Techposts/TankSync/docs/firmware/screenshots/flasher/flasher-1.png

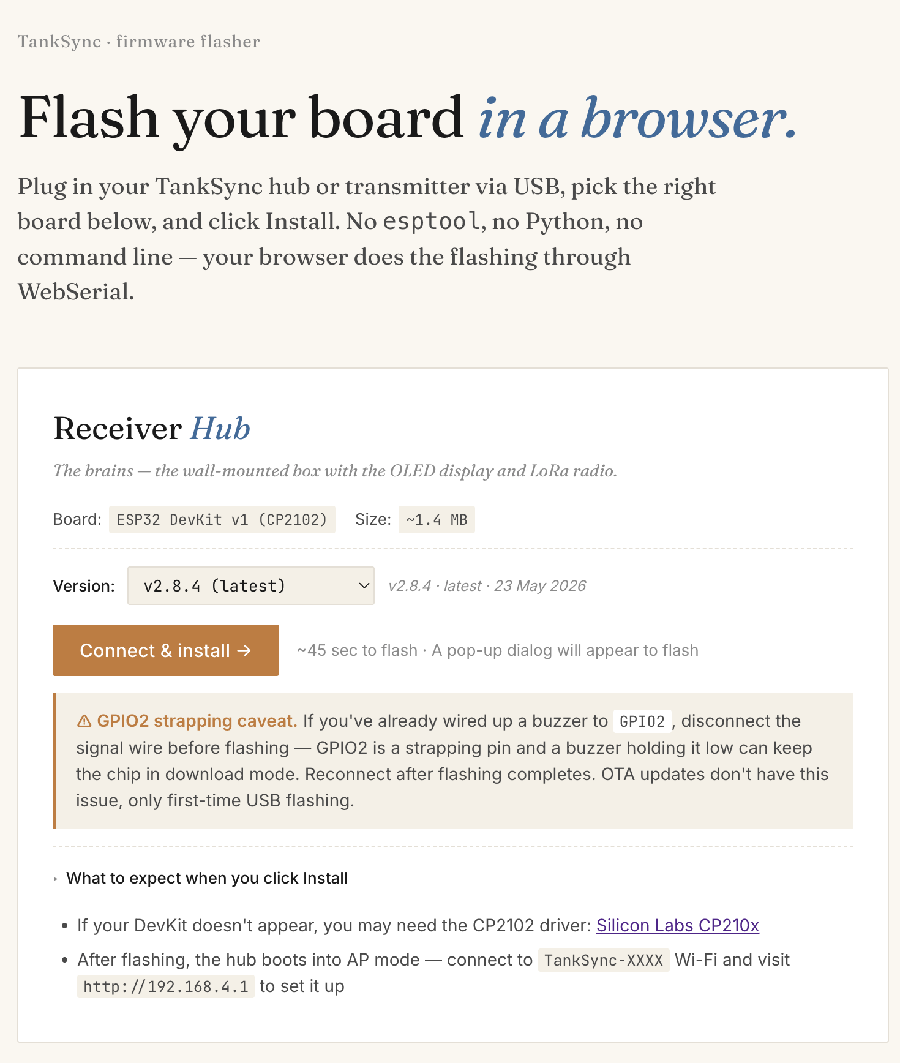
docs/firmware/screenshots/flasher/flasher-1.png
