Techposts/TankSync/docs/firmware/screenshots/flasher/flasher-2.png

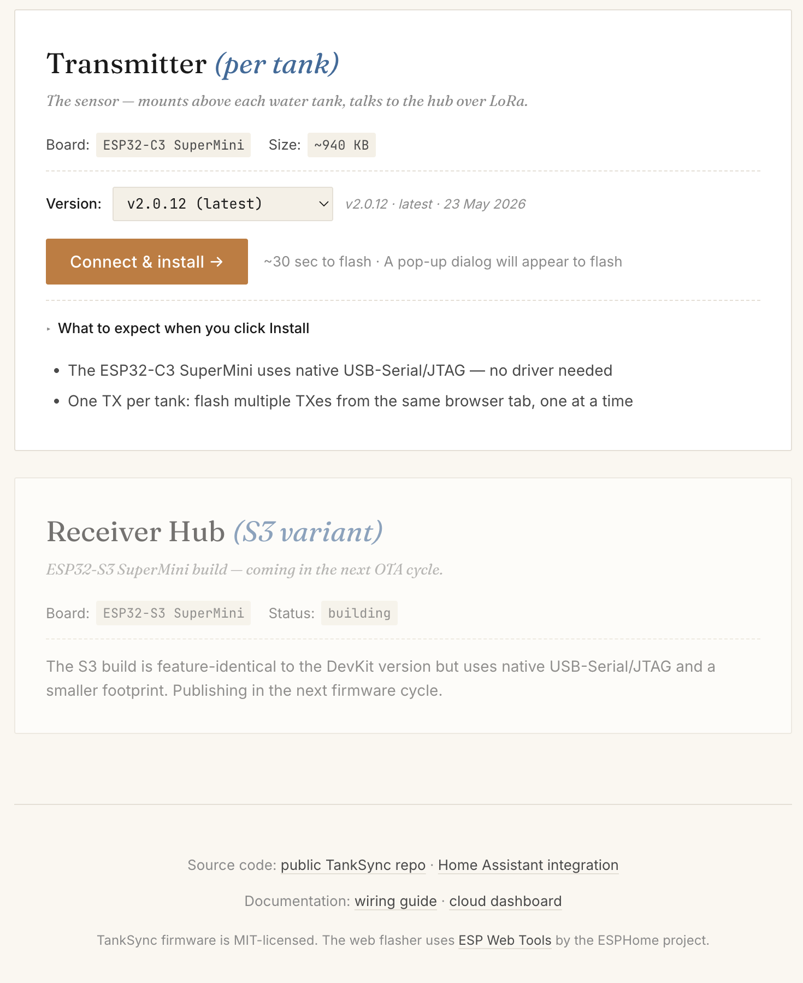
docs/firmware/screenshots/flasher/flasher-2.png
