Techposts/TankSync/docs/firmware/screenshots/pwa/alerts-feed-dark.png

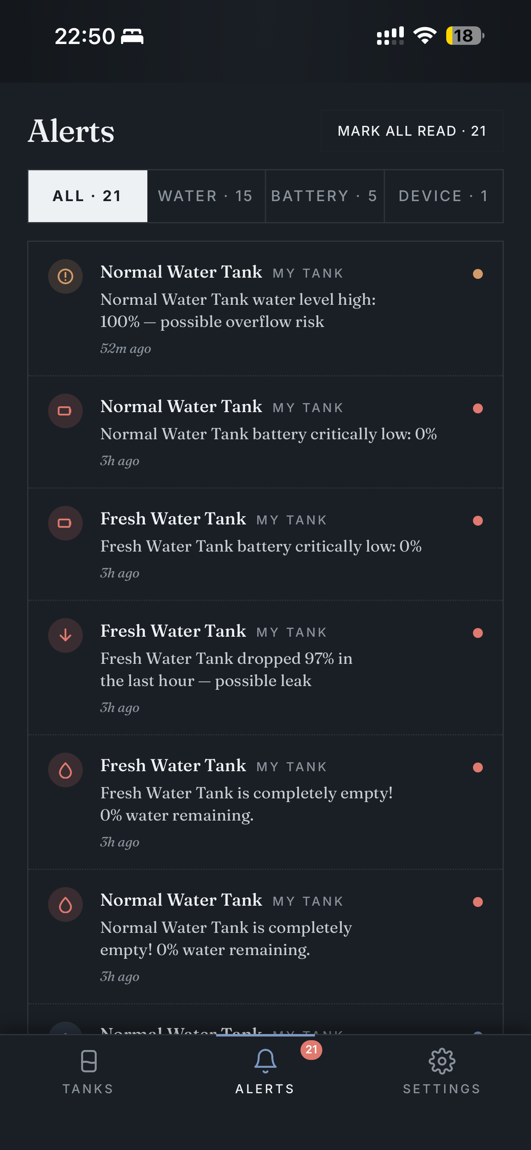
docs/firmware/screenshots/pwa/alerts-feed-dark.png
