Techposts/TankSync/docs/firmware/screenshots/pwa/alerts-feed-light.png

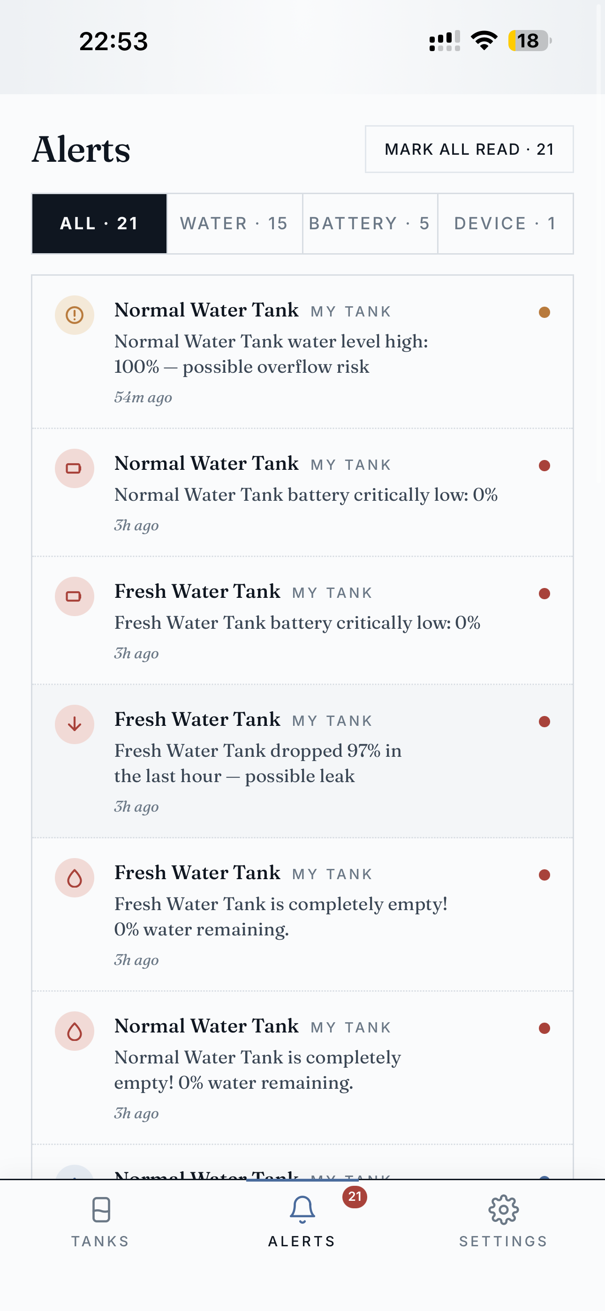
docs/firmware/screenshots/pwa/alerts-feed-light.png
