Techposts/TankSync/docs/firmware/screenshots/pwa/dashboard-light.png

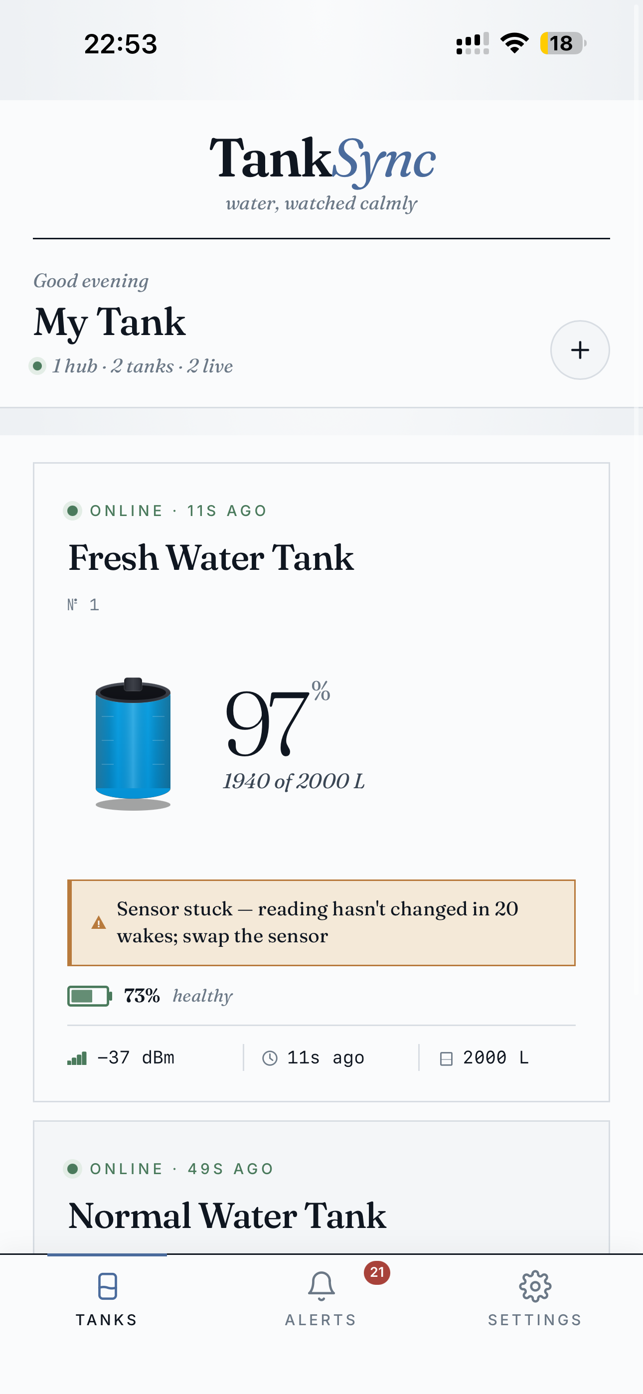
docs/firmware/screenshots/pwa/dashboard-light.png
