Techposts/TankSync/docs/firmware/screenshots/pwa/dashboard-sensor-stuck-warning.png

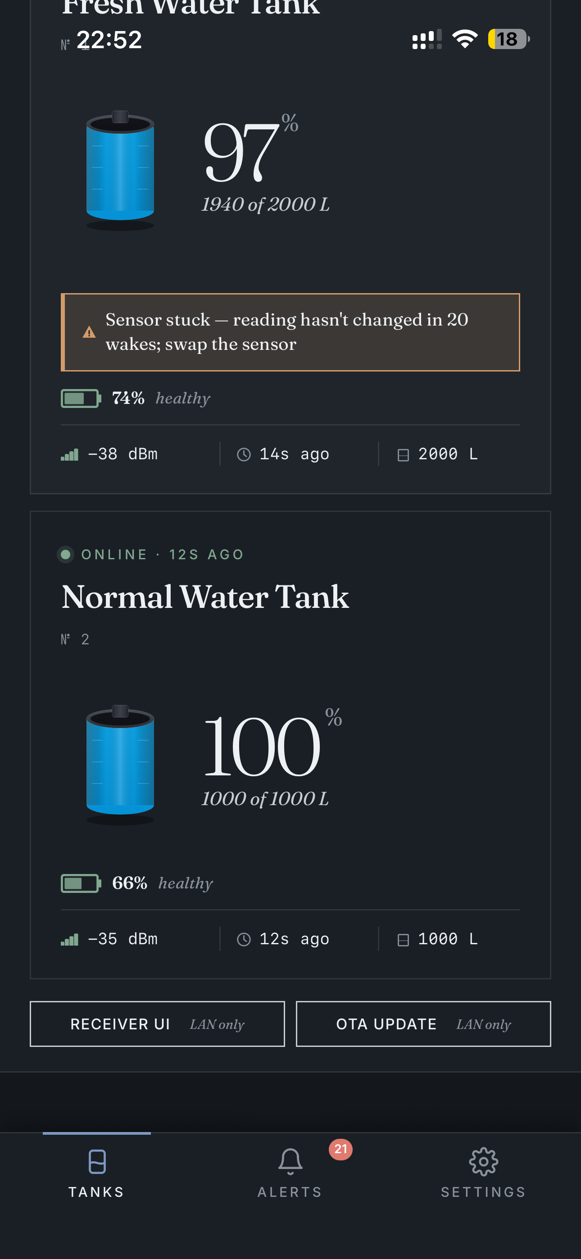
docs/firmware/screenshots/pwa/dashboard-sensor-stuck-warning.png
