Techposts/TankSync/docs/firmware/screenshots/pwa/firmware-update-page.png

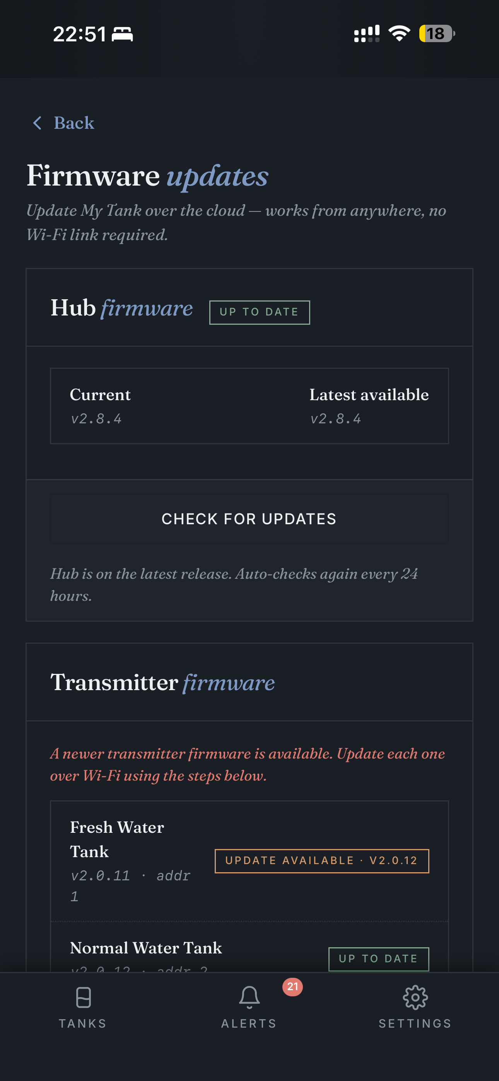
docs/firmware/screenshots/pwa/firmware-update-page.png
