Techposts/TankSync/docs/firmware/screenshots/pwa/settings-hub-led-buzzer.png

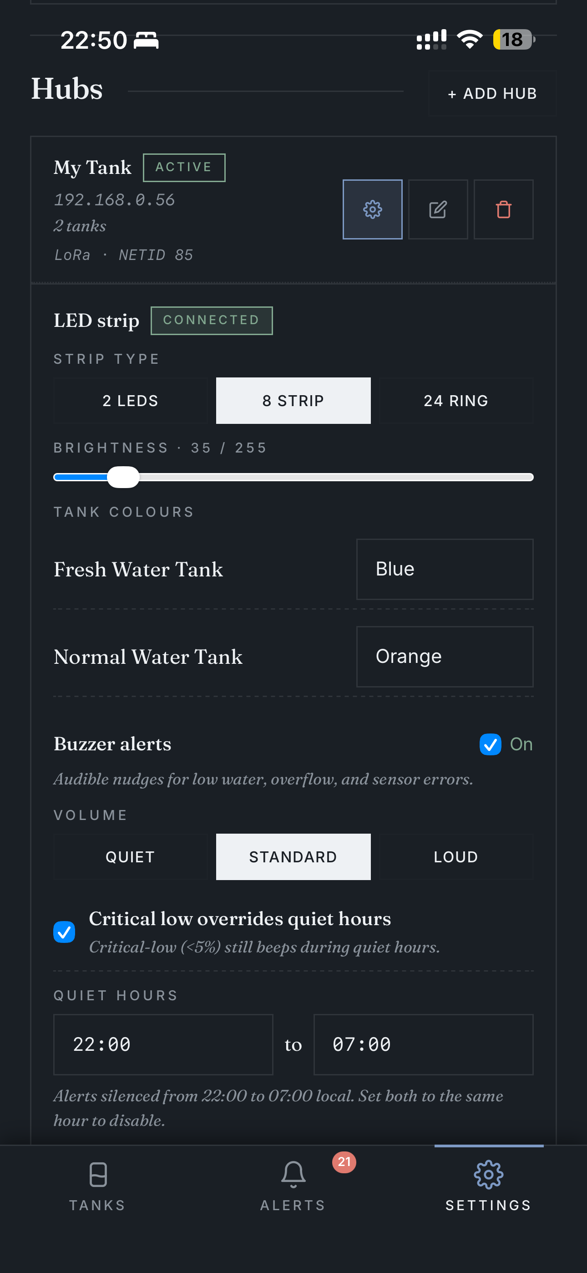
docs/firmware/screenshots/pwa/settings-hub-led-buzzer.png
