Techposts/TankSync/docs/firmware/screenshots/pwa/settings-localnet-firmware-about-dark.png

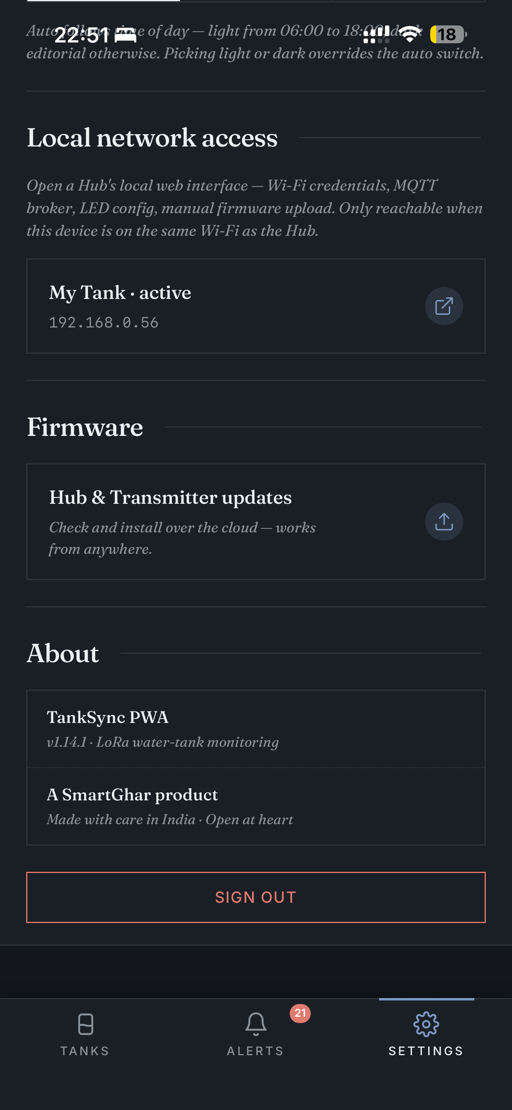
docs/firmware/screenshots/pwa/settings-localnet-firmware-about-dark.png
