Techposts/TankSync/docs/firmware/screenshots/pwa/settings-localnet-firmware-about-light.png

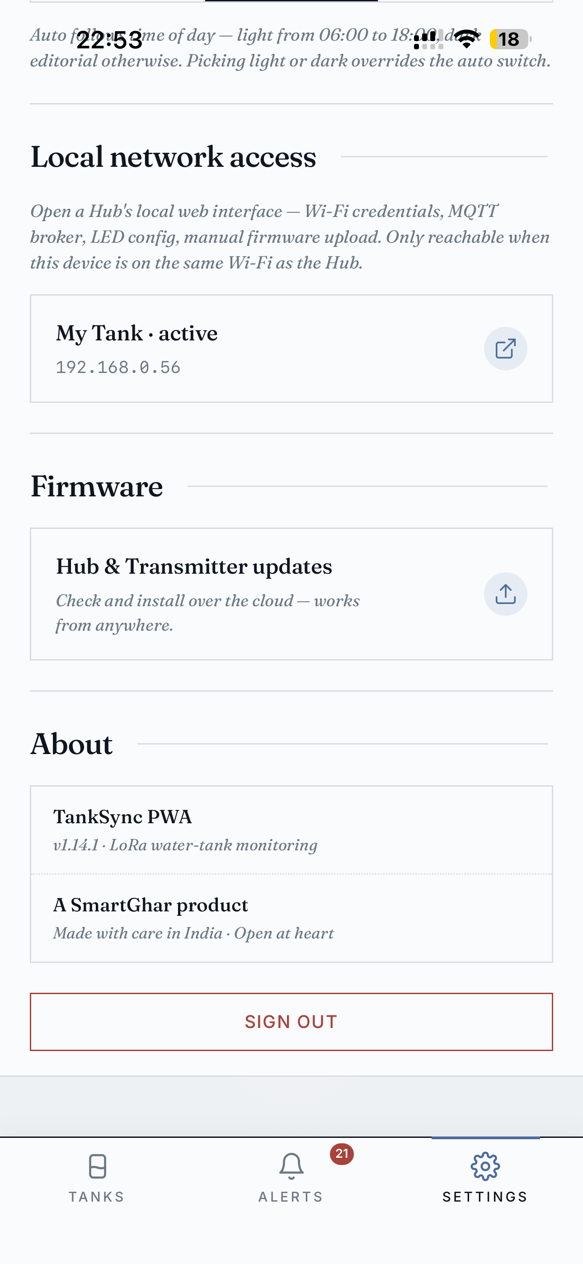
docs/firmware/screenshots/pwa/settings-localnet-firmware-about-light.png
