Techposts/TankSync/docs/firmware/screenshots/pwa/settings-profile-plan.png

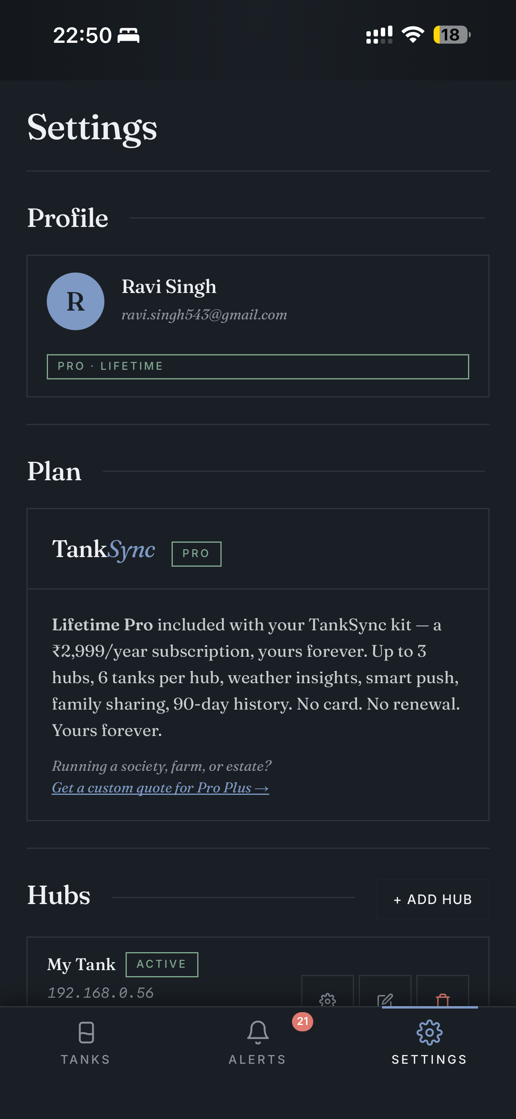
docs/firmware/screenshots/pwa/settings-profile-plan.png
