Techposts/TankSync/docs/firmware/screenshots/pwa/settings-support-notifications-appearance.png

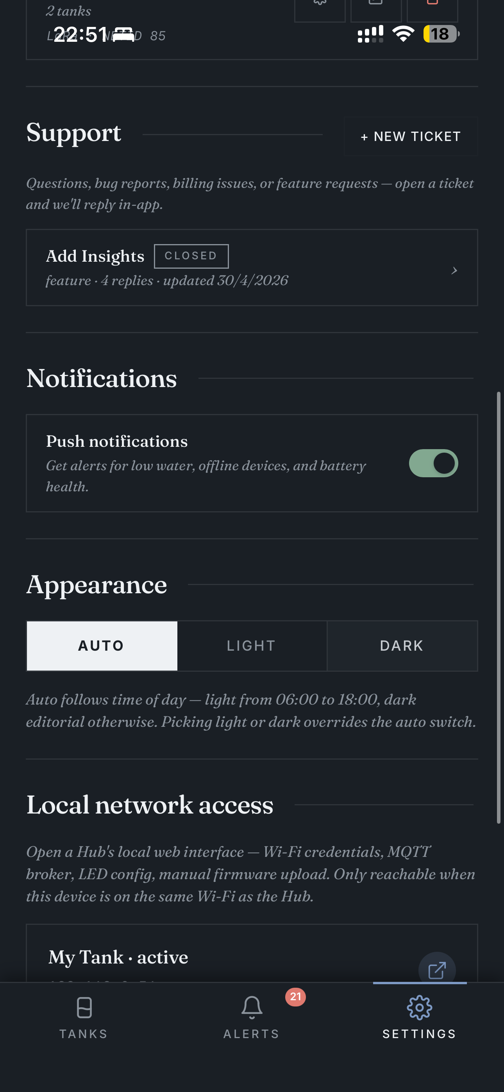
docs/firmware/screenshots/pwa/settings-support-notifications-appearance.png
