Techposts/TankSync/docs/firmware/screenshots/pwa/tank-detail-power-telemetry.png

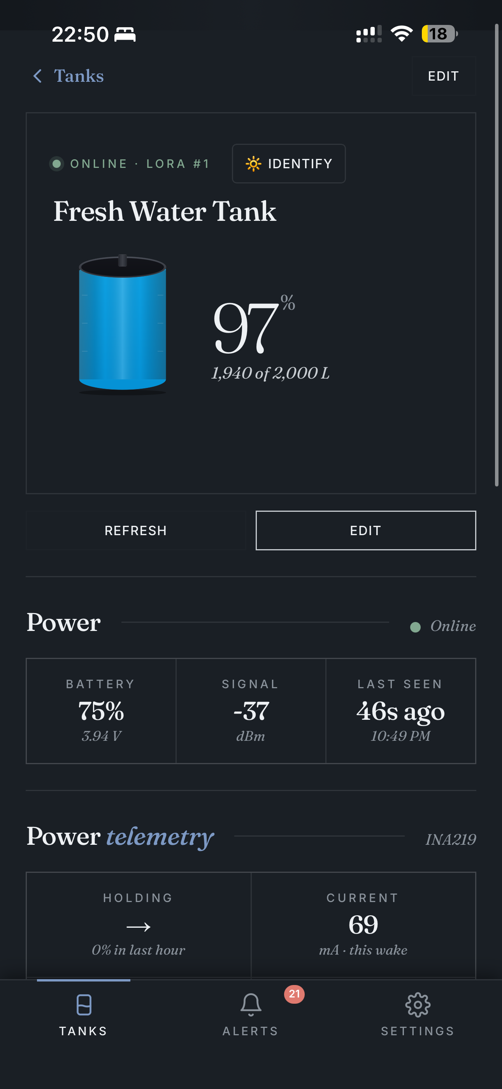
docs/firmware/screenshots/pwa/tank-detail-power-telemetry.png
