Techposts/TankSync/docs/firmware/screenshots/webui/cloud-link-device-id.png

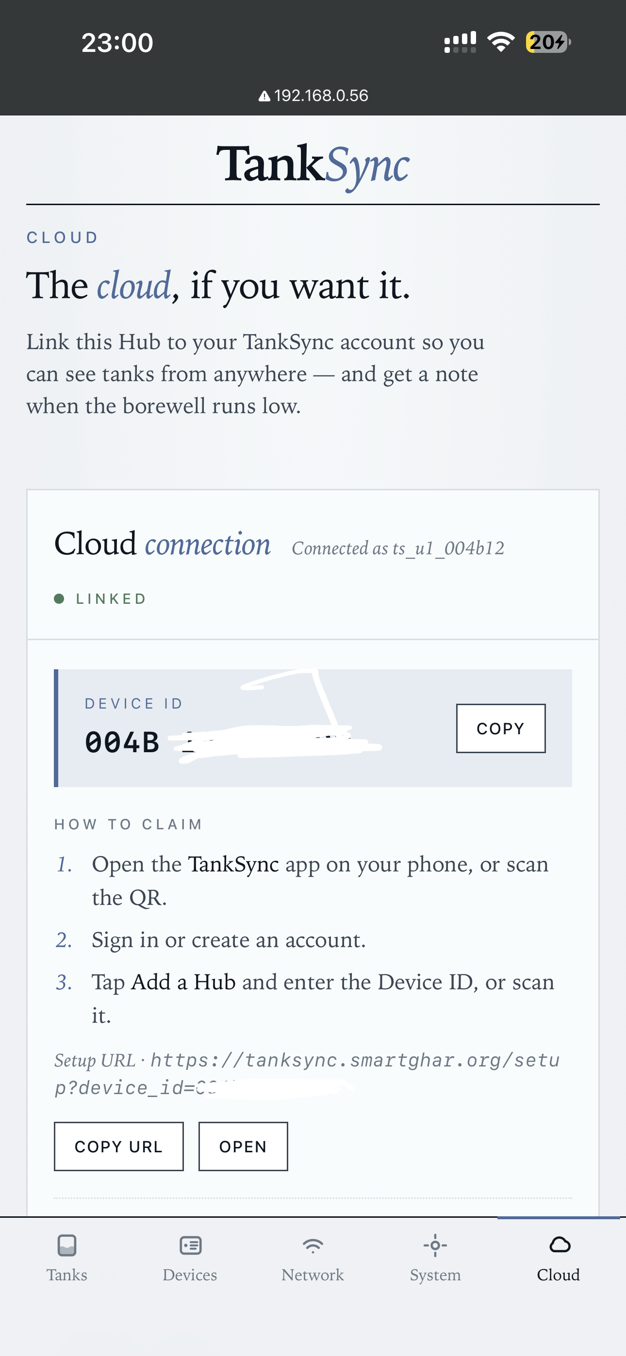
docs/firmware/screenshots/webui/cloud-link-device-id.png
