Techposts/TankSync/docs/firmware/screenshots/webui/cloud-link-qr-unlink.png

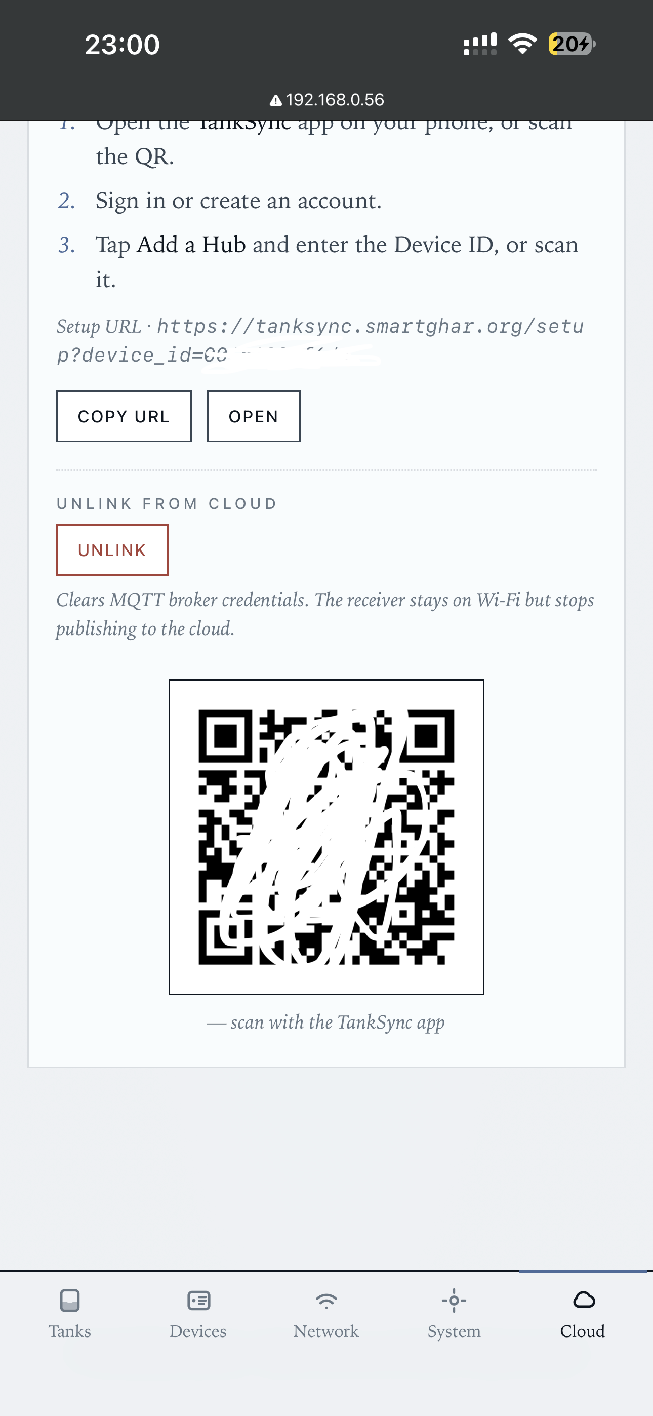
docs/firmware/screenshots/webui/cloud-link-qr-unlink.png
