Techposts/TankSync/docs/firmware/screenshots/webui/devices-list.png

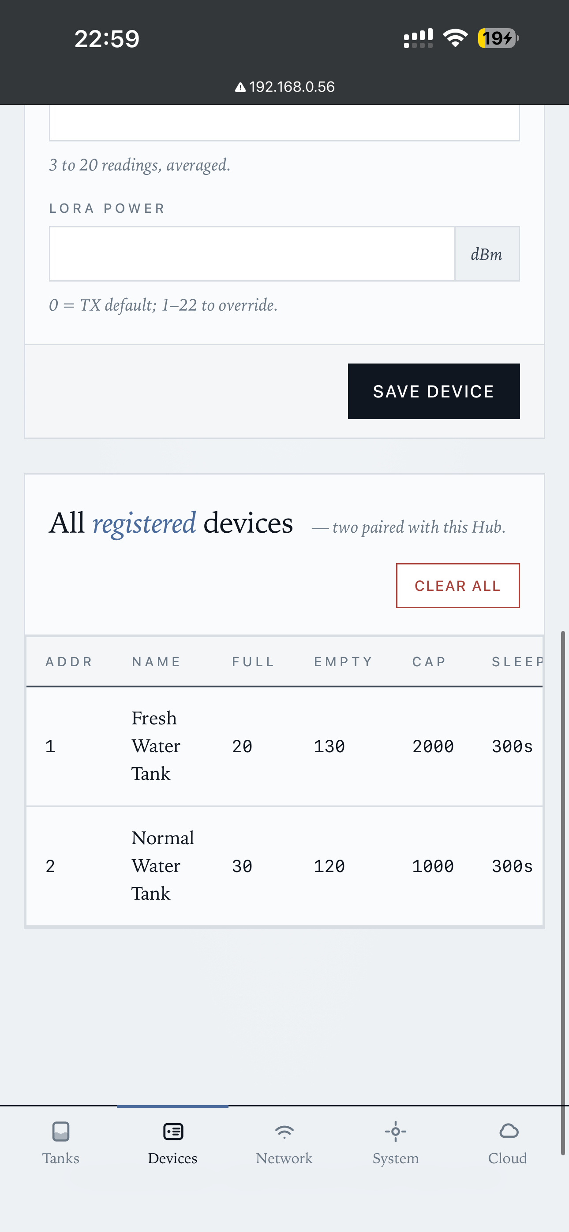
docs/firmware/screenshots/webui/devices-list.png
