Techposts/TankSync/docs/firmware/screenshots/webui/devices-pair-edit-form.png

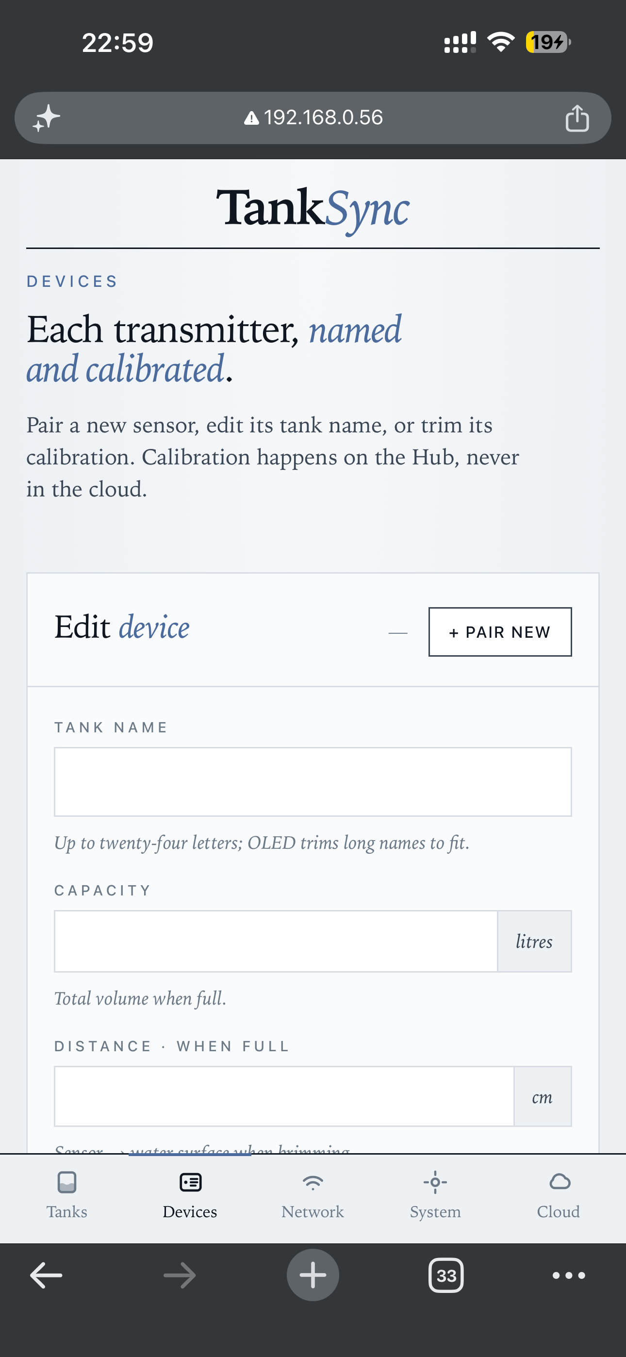
docs/firmware/screenshots/webui/devices-pair-edit-form.png
