Techposts/TankSync/docs/firmware/screenshots/webui/network-lora.png

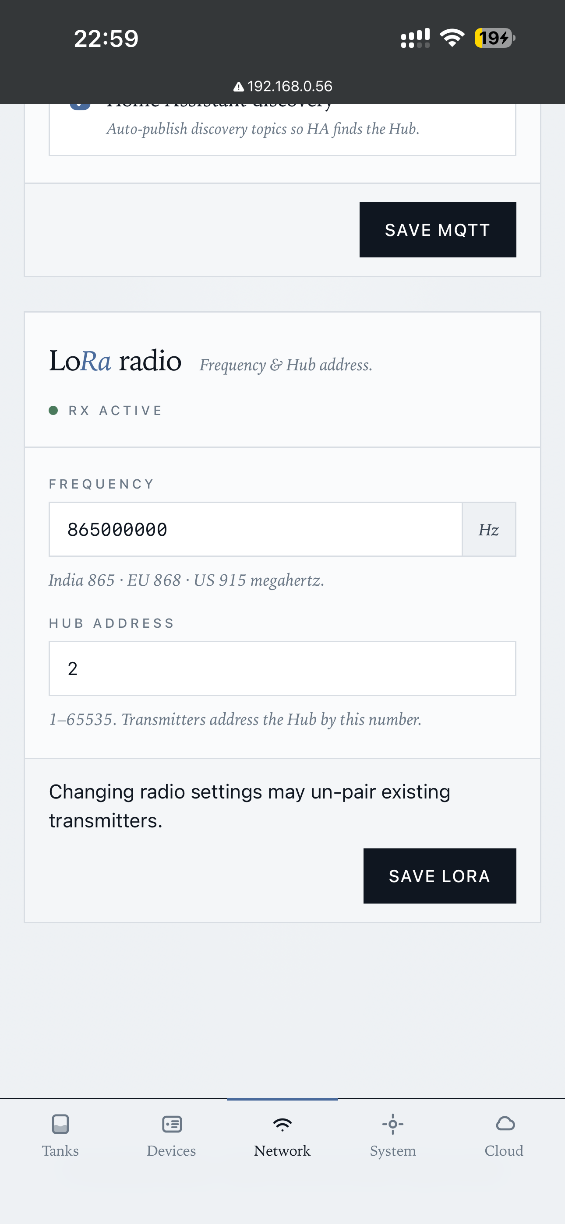
docs/firmware/screenshots/webui/network-lora.png
