Techposts/TankSync/docs/firmware/screenshots/webui/network-mqtt.png

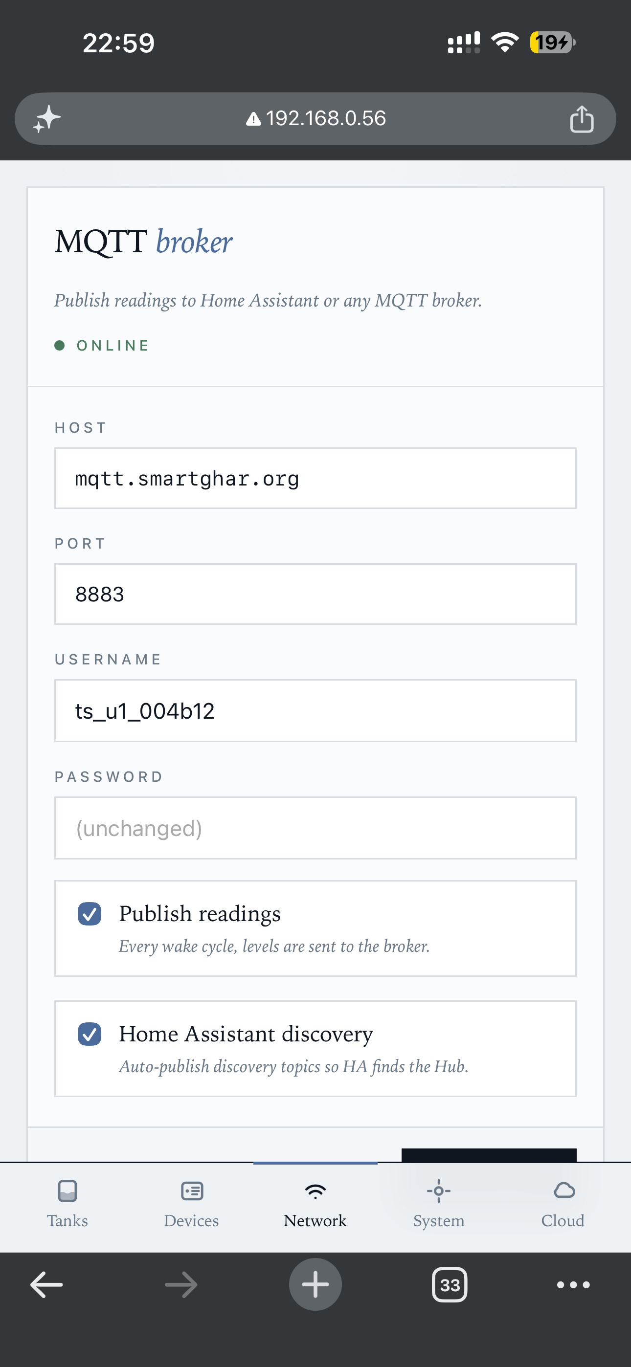
docs/firmware/screenshots/webui/network-mqtt.png
