Techposts/TankSync/docs/firmware/screenshots/webui/network-wifi.png

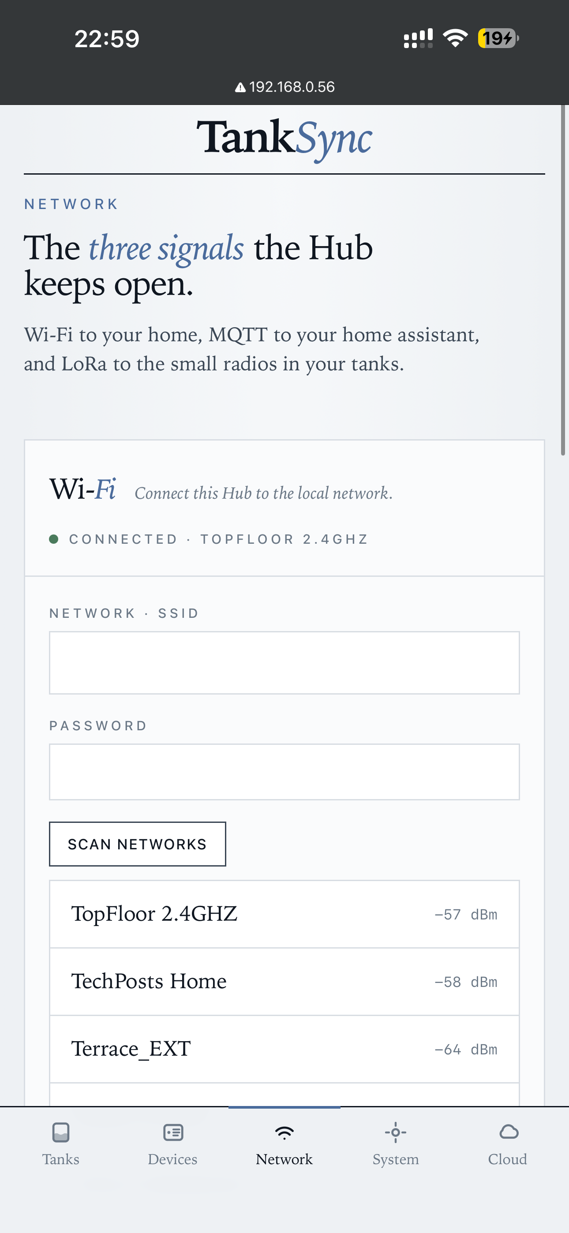
docs/firmware/screenshots/webui/network-wifi.png
