Techposts/TankSync/docs/firmware/screenshots/webui/system-buzzer-alerts.png

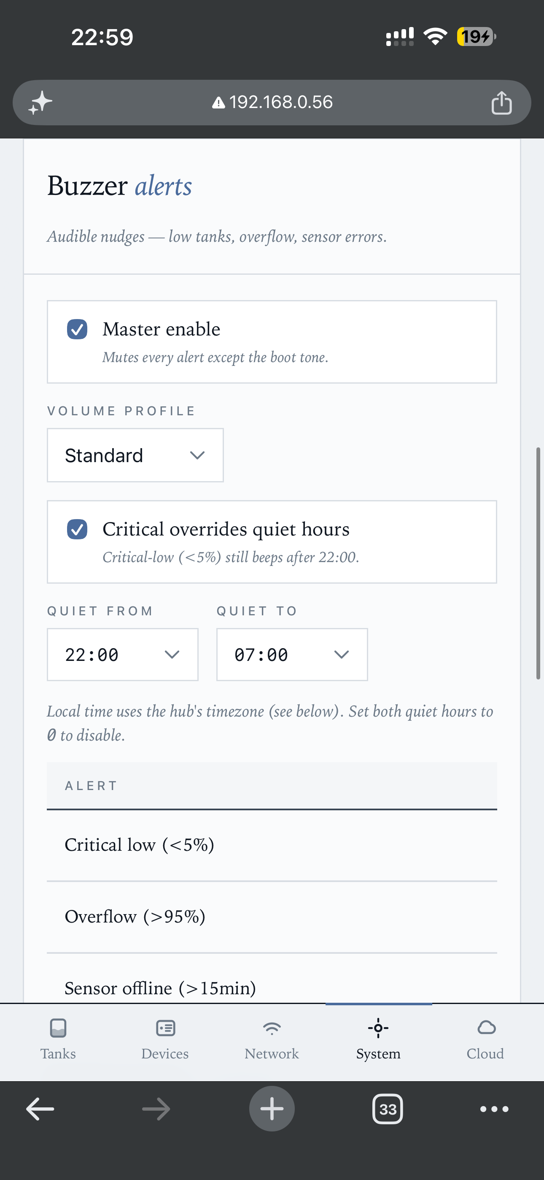
docs/firmware/screenshots/webui/system-buzzer-alerts.png
