Techposts/TankSync/docs/firmware/screenshots/webui/system-display-oled.png

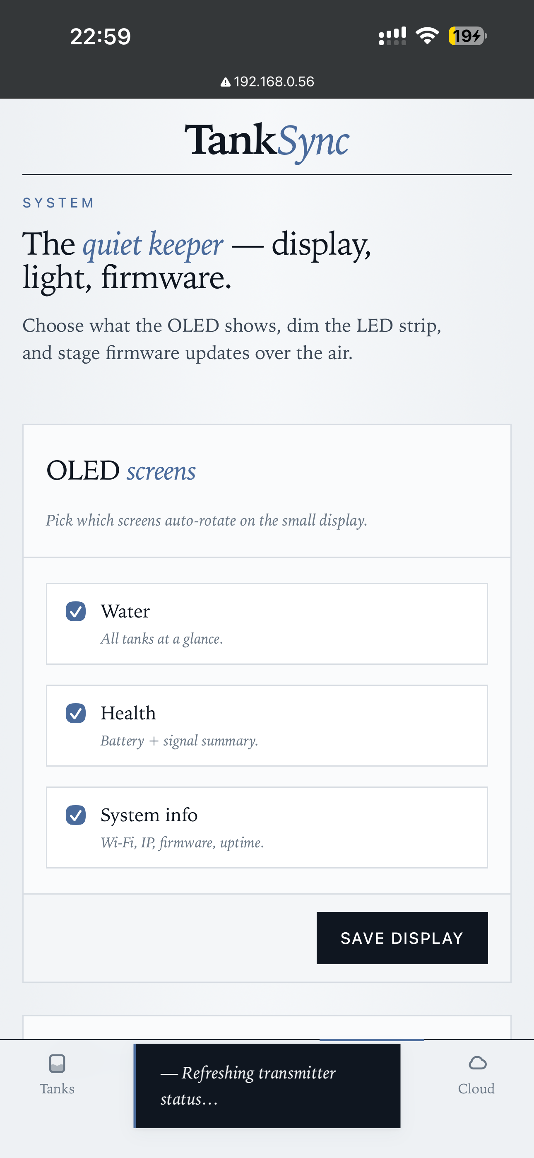
docs/firmware/screenshots/webui/system-display-oled.png
