Techposts/TankSync/docs/firmware/screenshots/webui/system-firmware-updates.png

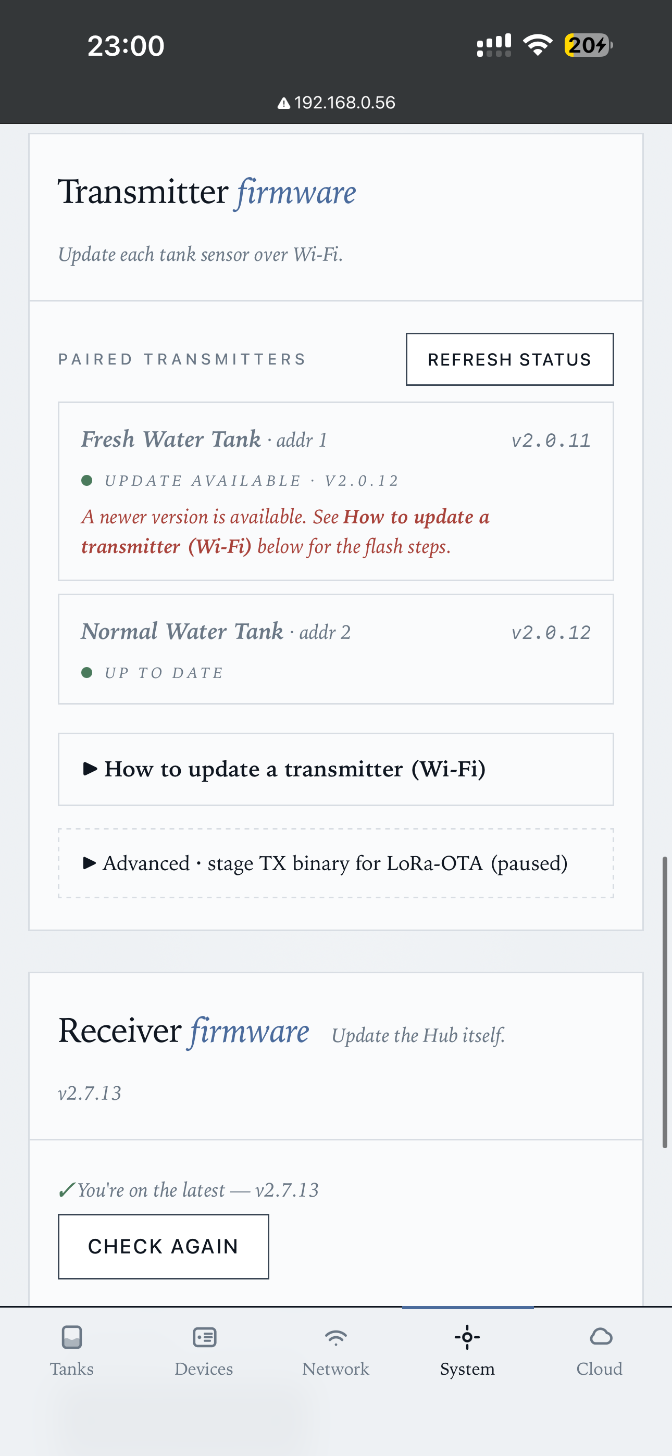
docs/firmware/screenshots/webui/system-firmware-updates.png
