Techposts/TankSync/docs/firmware/screenshots/webui/system-led-strip.png

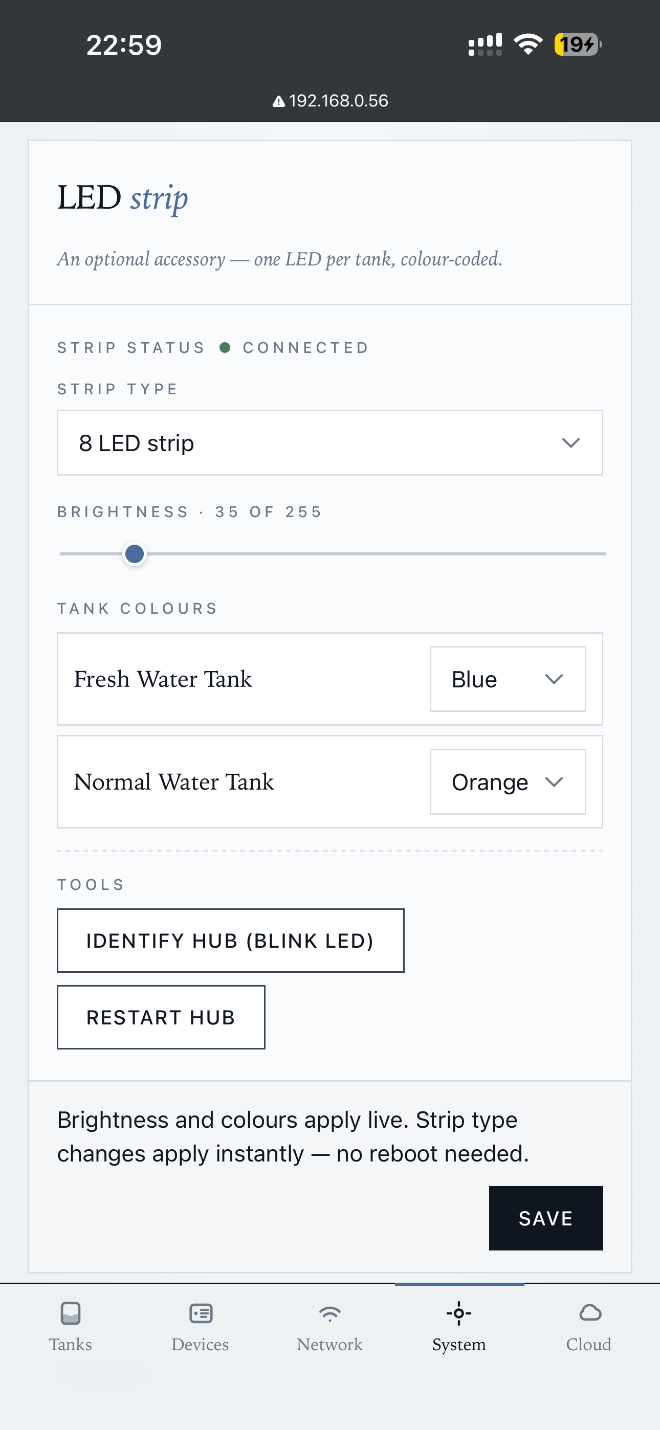
docs/firmware/screenshots/webui/system-led-strip.png
