Techposts/TankSync/docs/firmware/screenshots/webui/tanks-detail-steady-draw.png

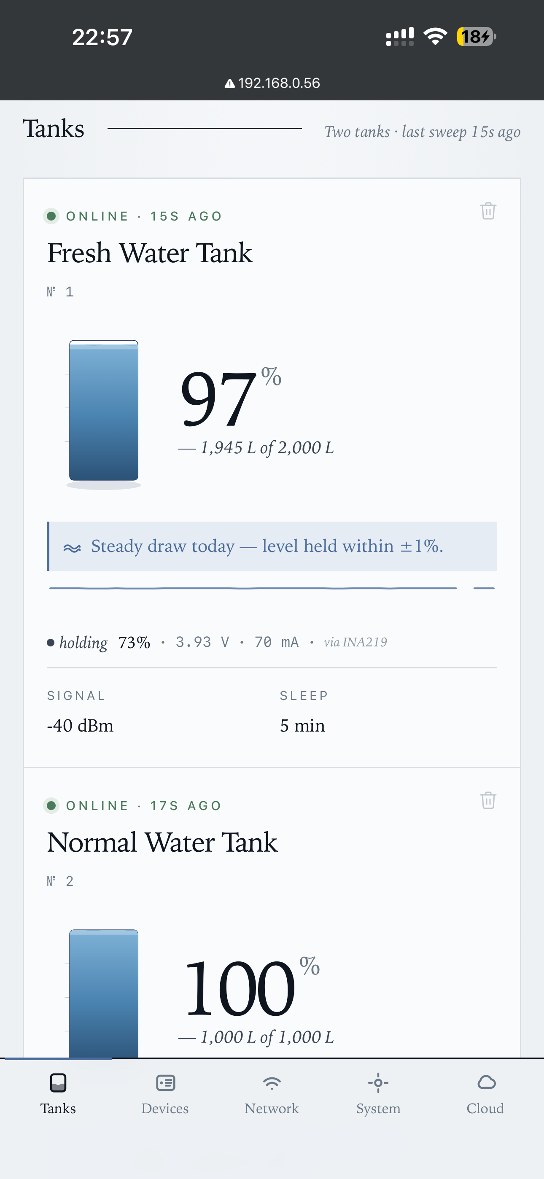
docs/firmware/screenshots/webui/tanks-detail-steady-draw.png
