Techposts/TankSync/docs/firmware/screenshots/webui/tanks-things-worth-knowing.png

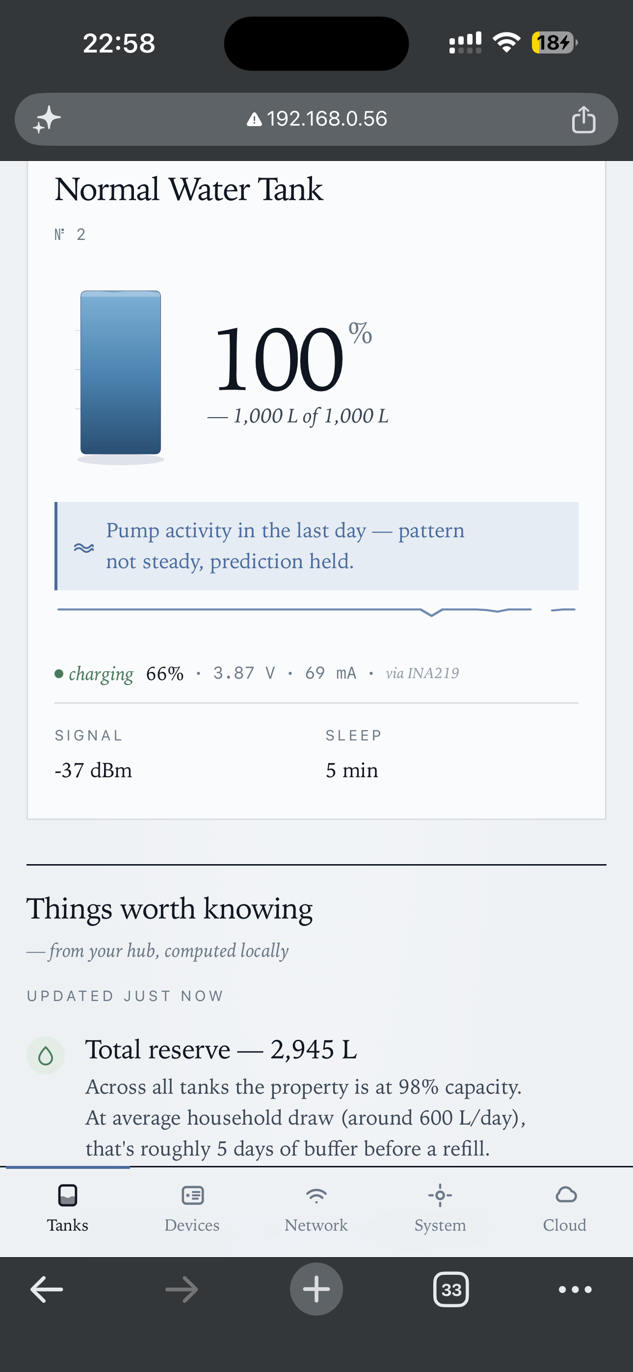
docs/firmware/screenshots/webui/tanks-things-worth-knowing.png
