Techposts/TankSync/docs/firmware/screenshots/webui/things-worth-knowing-detail.png

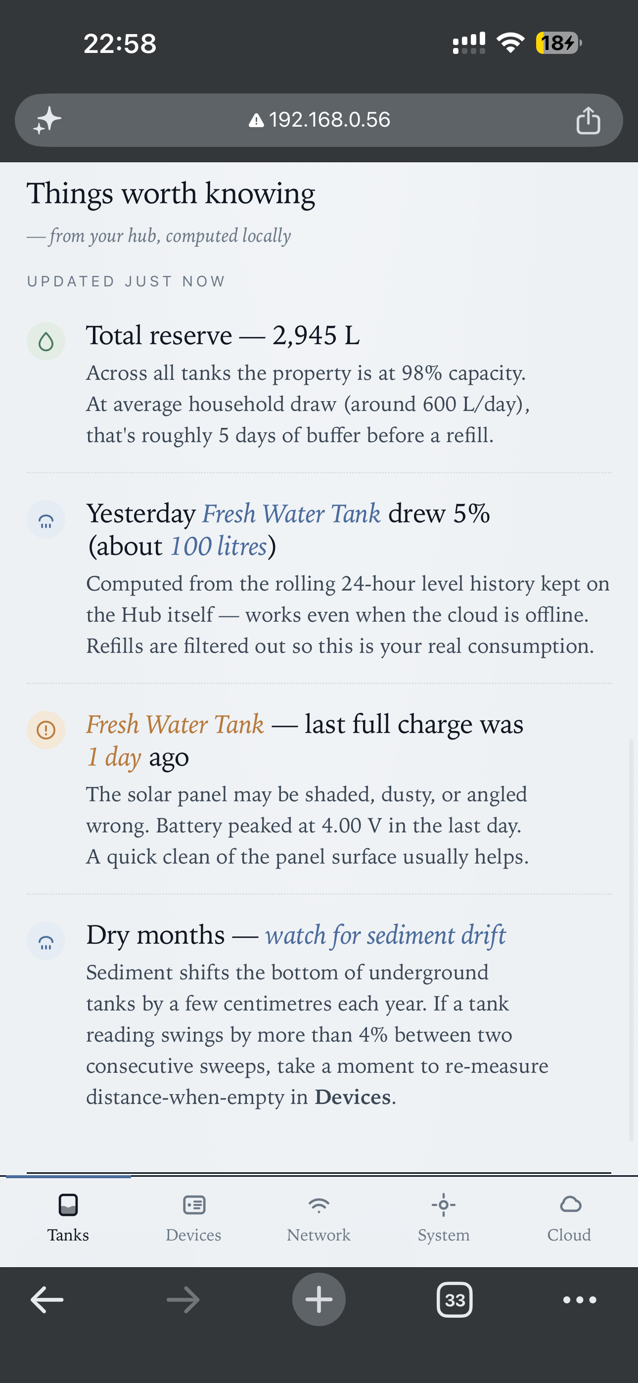
docs/firmware/screenshots/webui/things-worth-knowing-detail.png
