Techposts/TankSync/docs/images/flashing.jpg

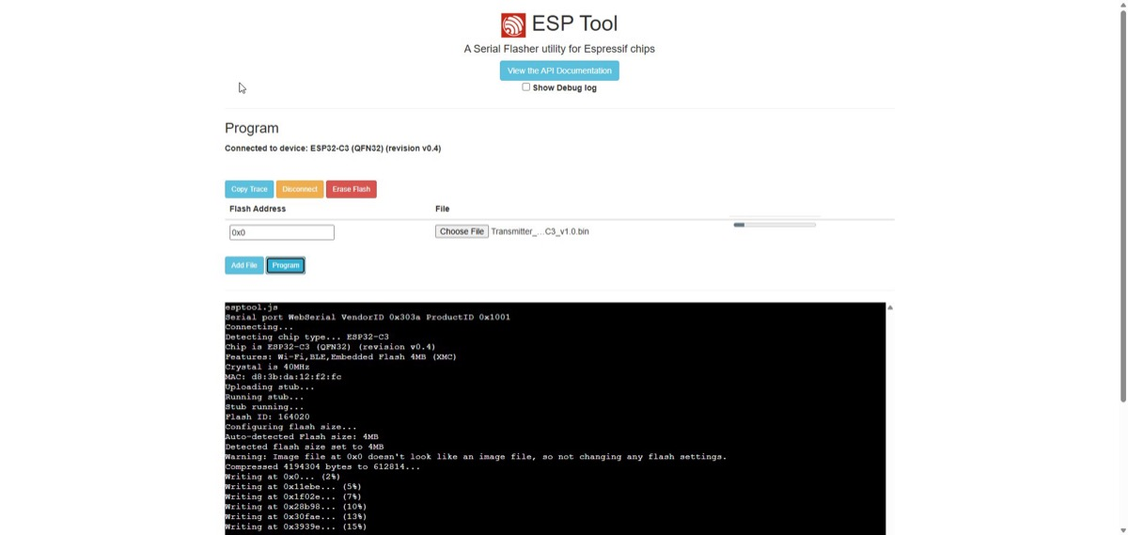
docs/images/flashing.jpg
