Techposts/TankSync/docs/images/home-assistant-dashboard.jpg

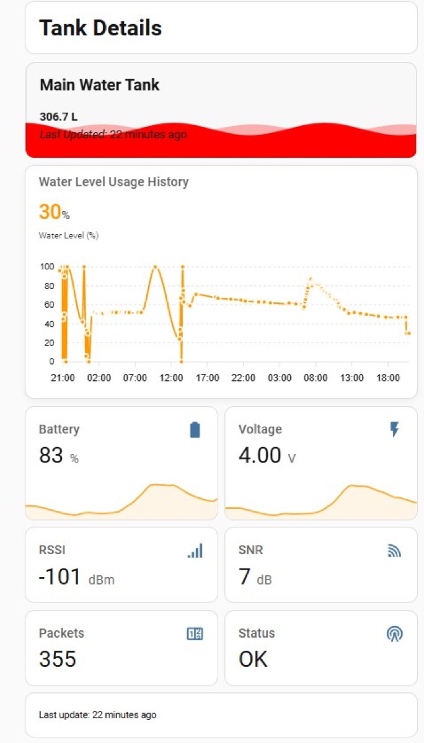
docs/images/home-assistant-dashboard.jpg
