Techposts/TankSync/docs/images/home-assistant-mqtt.jpg

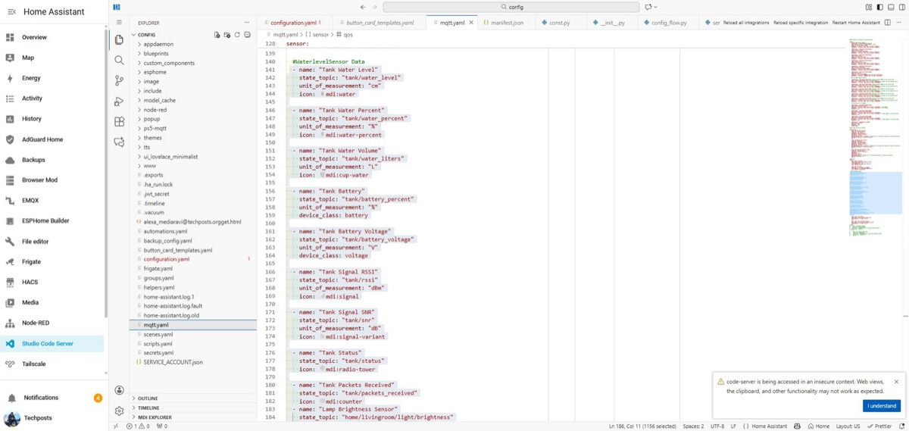
docs/images/home-assistant-mqtt.jpg
