Techposts/TankSync/docs/images/receiver.jpg

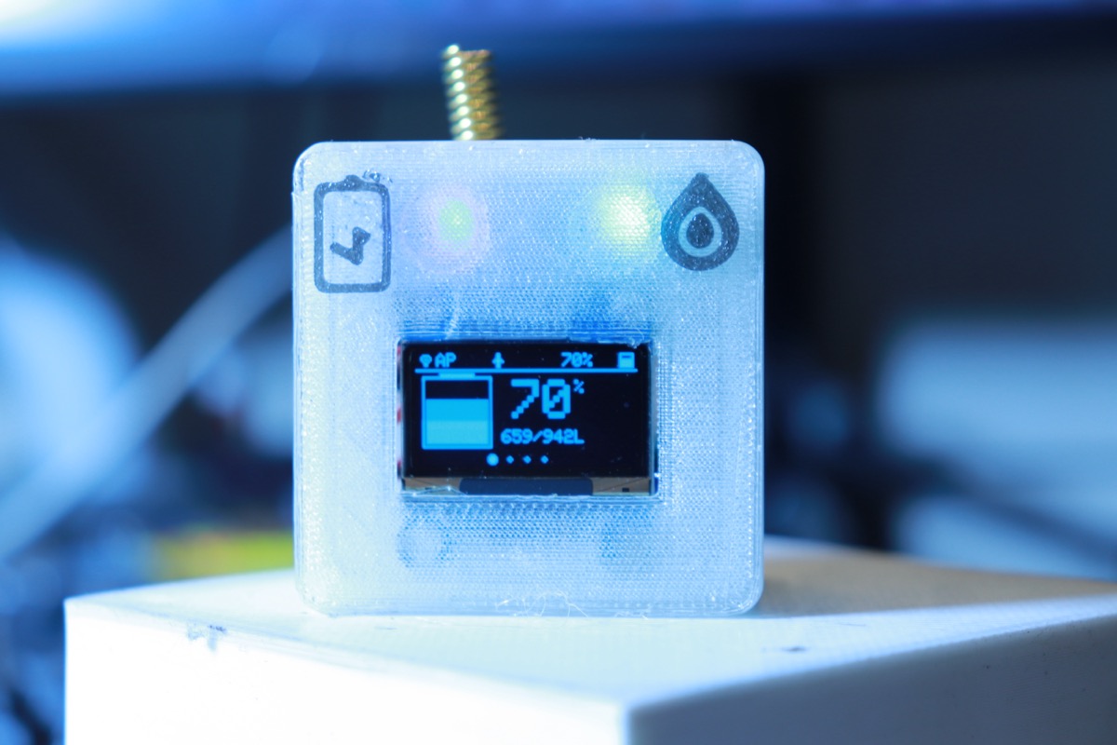
docs/images/receiver.jpg
