Techposts/TankSync/docs/images/selecting-board.jpg

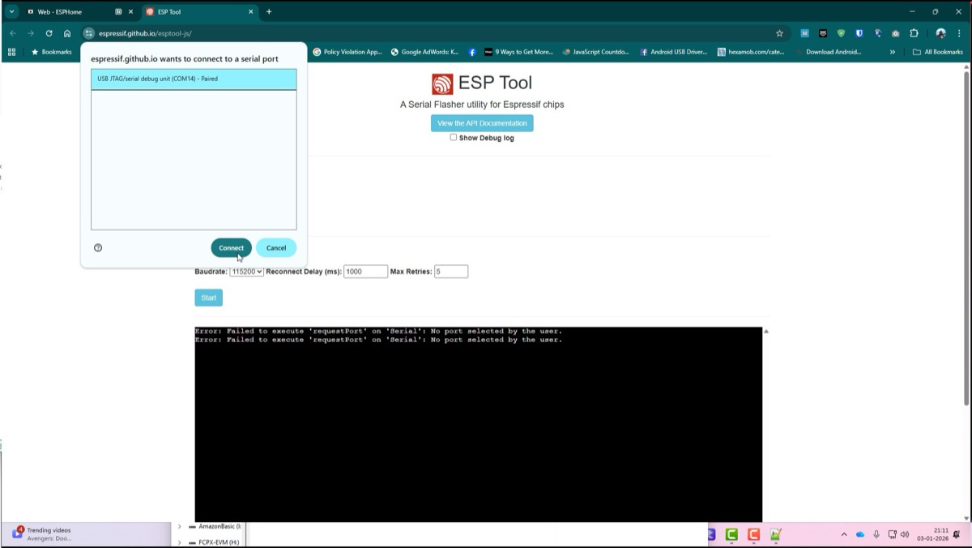
docs/images/selecting-board.jpg
