Techposts/TankSync/docs/images/transmitter.jpg

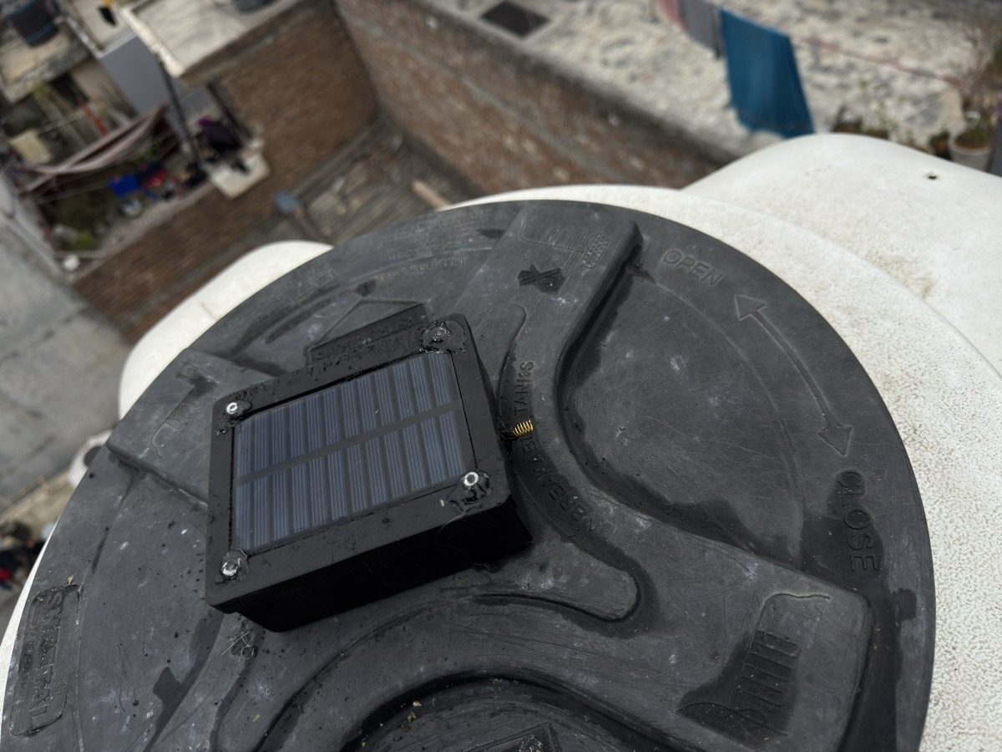
docs/images/transmitter.jpg
