Techposts/TankSync/hardware/pcb/rx-schematic.png

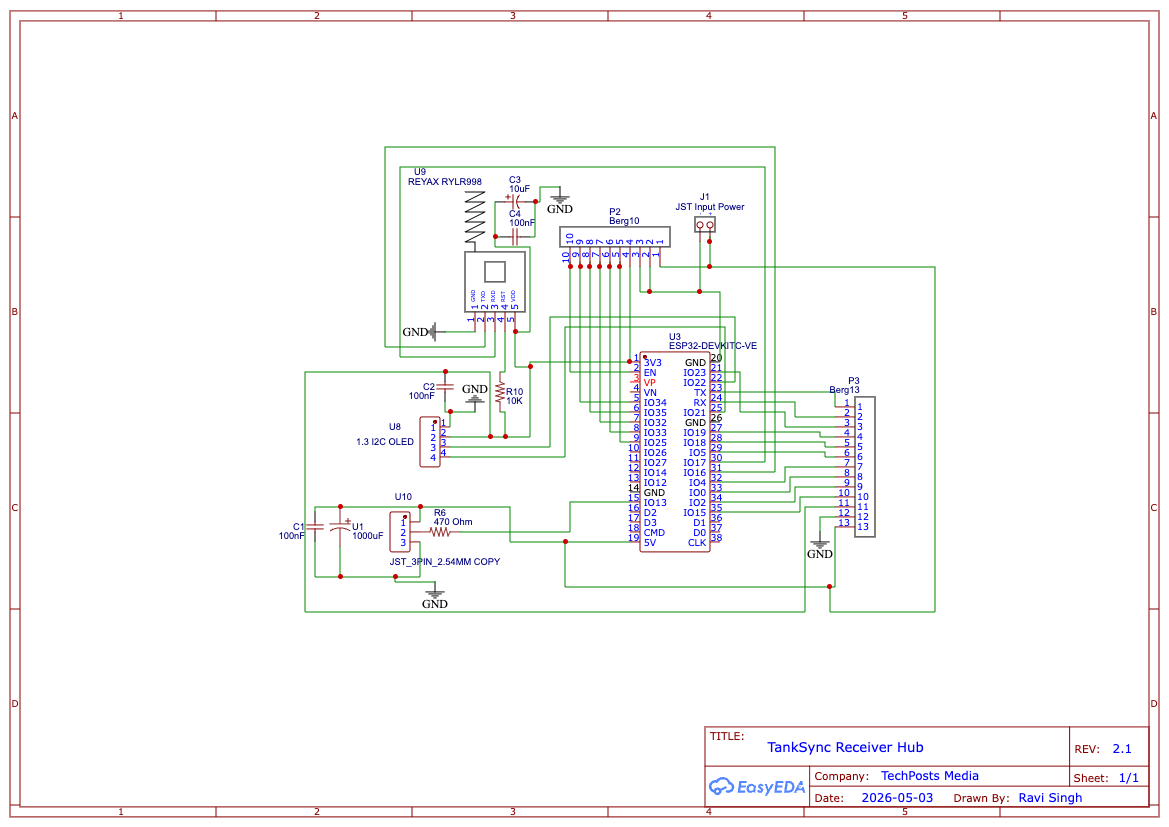
hardware/pcb/rx-schematic.png
