Techposts/TankSync/hardware/pcb/tx-schematic.png

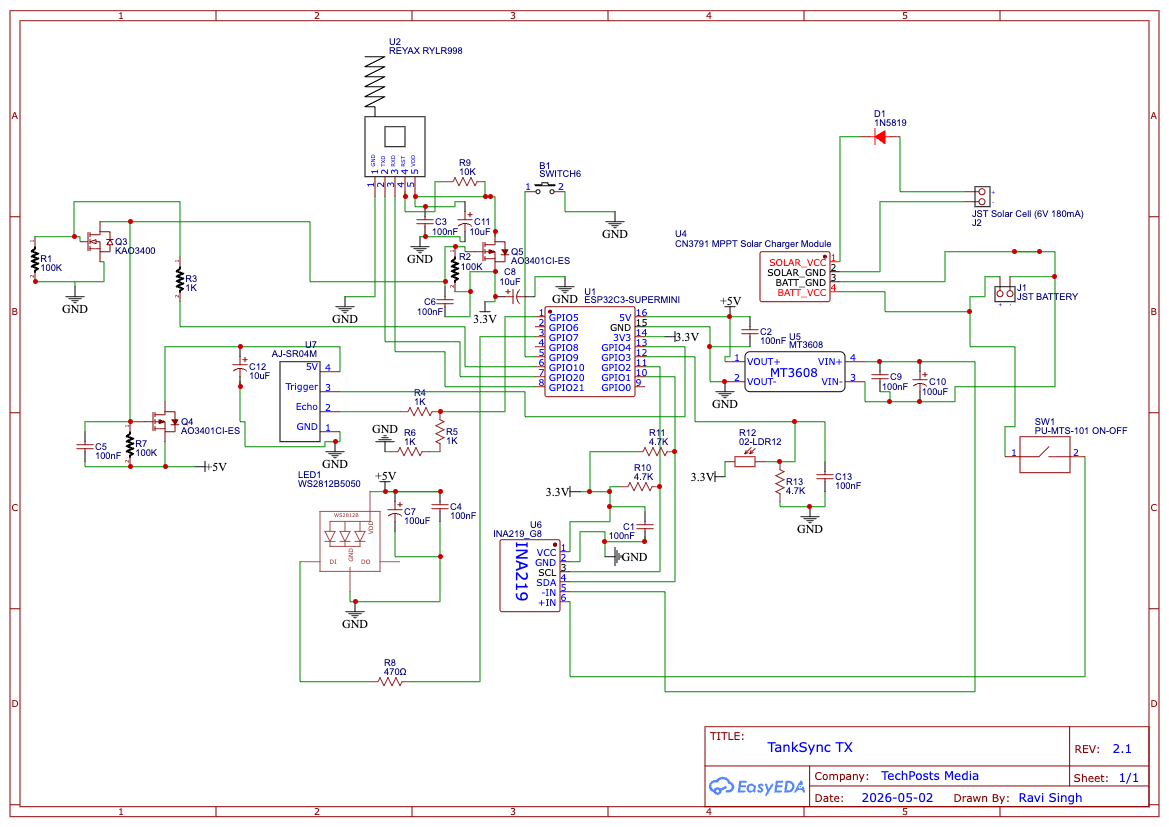
hardware/pcb/tx-schematic.png
