Techposts/TankSync/docs/firmware/screenshots/pwa/tank-detail-battery-history.png

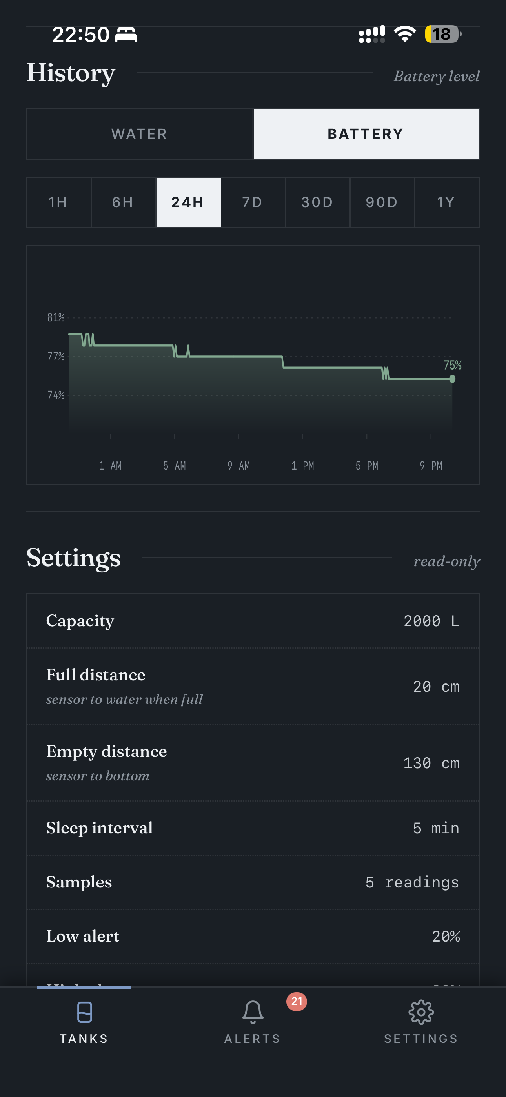
docs/firmware/screenshots/pwa/tank-detail-battery-history.png
