Techposts/TankSync/firmware/Receiver-ESP32-DevKit/components/led_ws2812/led_ws2812.c

/**
 * led_ws2812 - RMT-based WS2812B driver
 *
 * Uses ESP-IDF 5.x RMT TX channel with the led_strip encoder pattern.
 * WS2812B timing: T0H=350ns, T0L=800ns, T1H=700ns, T1L=600ns, Reset>50us
 * At 10MHz RMT clock: 1 tick = 100ns
 */

#include "led_ws2812.h"
#include "driver/rmt_tx.h"
#include "driver/rmt_encoder.h"
#include "esp_log.h"
#include "freertos/FreeRTOS.h"
#include "freertos/semphr.h"
#include "freertos/task.h"
#include <string.h>
#include <math.h>

static const char *TAG = "led_ws2812";

#define RMT_RESOLUTION_HZ   10000000    // 10 MHz → 100ns per tick
#define MAX_LEDS            24

// WS2812B bit timings in RMT ticks (1 tick = 100ns)
#define T0H  4   // 400ns high for '0'
#define T0L  8   // 800ns low  for '0'
#define T1H  7   // 700ns high for '1'
#define T1L  6   // 600ns low  for '1'
#define RESET_US 80  // >50µs reset

static rmt_channel_handle_t rmt_chan = NULL;
static rmt_encoder_handle_t rmt_enc  = NULL;
static rmt_transmit_config_t tx_cfg = { .loop_count = 0 };

static led_color_t s_leds[MAX_LEDS];
static int         s_num_leds  = 0;
static uint8_t     s_brightness = 50;
static led_effect_t s_current_effect = LED_EFFECT_NONE;
static SemaphoreHandle_t s_led_mutex = NULL;  // protects rmt_transmit + s_leds

// Driver health: 2.6.2 — strip can disconnect/reconnect at runtime; never permanent-disable
static bool        s_initialized = false;
static bool        s_strip_present = false;
static int         s_rmt_fail_count = 0;
static TickType_t  s_last_fail_tick = 0;
#define LED_FAIL_BACKOFF_THRESHOLD 5
#define LED_RETRY_INTERVAL_TICKS pdMS_TO_TICKS(5000)

// ── Background effect task ───────────────────────────────────────────────────
static void led_effect_task(void *arg) {
    uint32_t step = 0;
    for (;;) {
        if (s_current_effect == LED_EFFECT_NONE) {
            vTaskDelay(pdMS_TO_TICKS(100));
            continue;
        }

        switch (s_current_effect) {
            case LED_EFFECT_PULSE_AMBER: {
                // Sinusoidal pulse 10-100% of current brightness
                float val = 0.55f + 0.45f * sinf(step * 0.1f);
                uint8_t base_br = s_brightness;
                // Temporarily adjust brightness for build_rmt_buf inside led_show
                // Note: This is slightly hacky as it modifies global state, but works for single effect
                uint8_t old_br = s_brightness;
                s_brightness = (uint8_t)(old_br * val);
                for(int i=0; i<s_num_leds; i++) s_leds[i] = LED_AMBER;
                led_show();
                s_brightness = old_br;
                vTaskDelay(pdMS_TO_TICKS(30));
                break;
            }
            case LED_EFFECT_BLINK_RED:
                for(int i=0; i<s_num_leds; i++) s_leds[i] = (step % 2) ? LED_RED : LED_OFF;
                led_show();
                vTaskDelay(pdMS_TO_TICKS(250));
                break;
            case LED_EFFECT_BLINK_GREEN:
                for(int i=0; i<s_num_leds; i++) s_leds[i] = (step % 2) ? LED_GREEN : LED_OFF;
                led_show();
                vTaskDelay(pdMS_TO_TICKS(250));
                break;
            default: break;
        }
        step++;
    }
}

// ── Raw RMT symbols buffer: 24 bits × MAX_LEDS + reset ──────────────────────
// Each LED needs 24 rmt_symbol_word_t (one per bit, GRB order)
static rmt_symbol_word_t s_rmt_buf[MAX_LEDS * 24 + 1];

// ── Build the RMT symbol buffer from the LED color array ────────────────────
static void build_rmt_buf(void) {
    int pos = 0;
    for (int led = 0; led < s_num_leds; led++) {
        // WS2812B expects GRB byte order
        uint8_t raw[3] = {
            (uint8_t)(s_leds[led].g * s_brightness / 255),
            (uint8_t)(s_leds[led].r * s_brightness / 255),
            (uint8_t)(s_leds[led].b * s_brightness / 255),
        };
        for (int byte = 0; byte < 3; byte++) {
            for (int bit = 7; bit >= 0; bit--) {
                if ((raw[byte] >> bit) & 1) {
                    s_rmt_buf[pos].level0    = 1;
                    s_rmt_buf[pos].duration0 = T1H;
                    s_rmt_buf[pos].level1    = 0;
                    s_rmt_buf[pos].duration1 = T1L;
                } else {
                    s_rmt_buf[pos].level0    = 1;
                    s_rmt_buf[pos].duration0 = T0H;
                    s_rmt_buf[pos].level1    = 0;
                    s_rmt_buf[pos].duration1 = T0L;
                }
                pos++;
            }
        }
    }
    // Reset pulse: low for >50µs = 500 ticks at 10MHz, split across two durations
    s_rmt_buf[pos].level0    = 0;
    s_rmt_buf[pos].duration0 = 500;
    s_rmt_buf[pos].level1    = 0;
    s_rmt_buf[pos].duration1 = 0;  // marks end of symbols
    pos++;
    (void)pos;
}

esp_err_t led_init(int gpio_num, int num_leds, uint8_t brightness) {
    if (num_leds > MAX_LEDS) num_leds = MAX_LEDS;
    s_num_leds  = num_leds;
    s_brightness = brightness;
    memset(s_leds, 0, sizeof(s_leds));

    // Mutex first — must exist before any led_show() call so concurrent paths can't race.
    s_led_mutex = xSemaphoreCreateMutex();

    rmt_tx_channel_config_t chan_cfg = {
        .gpio_num            = gpio_num,
        .clk_src             = RMT_CLK_SRC_DEFAULT,
        .resolution_hz       = RMT_RESOLUTION_HZ,
        .mem_block_symbols   = 64,
        .trans_queue_depth   = 4,
        .flags.invert_out    = false,
        .flags.with_dma      = false,
    };
    esp_err_t err = rmt_new_tx_channel(&chan_cfg, &rmt_chan);
    if (err != ESP_OK) {
        ESP_LOGE(TAG, "rmt_new_tx_channel failed: %s", esp_err_to_name(err));
        return err;
    }

    // Use simple copy encoder — we supply pre-built RMT symbols
    rmt_copy_encoder_config_t enc_cfg = {};
    err = rmt_new_copy_encoder(&enc_cfg, &rmt_enc);
    if (err != ESP_OK) {
        ESP_LOGE(TAG, "rmt_new_copy_encoder failed: %s", esp_err_to_name(err));
        return err;
    }

    err = rmt_enable(rmt_chan);
    if (err != ESP_OK) {
        ESP_LOGE(TAG, "rmt_enable failed: %s", esp_err_to_name(err));
        return err;
    }

    s_initialized = true;

    // Blank all LEDs on init — also tests if LED is actually connected.
    // 2.6.2 fix: keep the RMT channel alive even if this initial test fails.
    // A loose wire on boot used to permanently disable the strip until reflash.
    build_rmt_buf();
    rmt_transmit(rmt_chan, rmt_enc, s_rmt_buf,
                 (s_num_leds * 24 + 1) * sizeof(rmt_symbol_word_t), &tx_cfg);
    esp_err_t tx_err = rmt_tx_wait_all_done(rmt_chan, pdMS_TO_TICKS(100));

    if (tx_err != ESP_OK) {
        ESP_LOGW(TAG, "WS2812B test transmit failed (%s) — strip may be disconnected. Will retry on next show().",
                 esp_err_to_name(tx_err));
        s_strip_present = false;
        s_rmt_fail_count = 1;
        s_last_fail_tick = xTaskGetTickCount();
    } else {
        ESP_LOGI(TAG, "WS2812B init OK: gpio=%d leds=%d brightness=%d",
                 gpio_num, num_leds, brightness);
        s_strip_present = true;
        s_rmt_fail_count = 0;
    }

    xTaskCreate(led_effect_task, "led_fx", 2048, NULL, 2, NULL);
    return ESP_OK;
}

// One-shot blink — used by /api/v1/hub/identify, /api/v1/devices/<id>/identify,
// and the MQTT cmd/ident_hub + cmd/ident_tank handlers. Five fast white pulses
// at 6 Hz beat the regular 4 FPS render loop visually; we don't bother
// restoring afterwards because the next render-loop tick reclaims the slot.
static void led_identify_task(void *arg) {
    int led_idx = (int)(intptr_t)arg;
    for (int i = 0; i < 5; i++) {
        led_set(led_idx, LED_WHITE); led_show();
        vTaskDelay(pdMS_TO_TICKS(150));
        led_set(led_idx, LED_OFF);   led_show();
        vTaskDelay(pdMS_TO_TICKS(150));
    }
    vTaskDelete(NULL);
}

void led_identify(int led_idx) {
    xTaskCreate(led_identify_task, "led_ident", 2048,
                (void *)(intptr_t)led_idx, 5, NULL);
}

void led_set_effect(led_effect_t effect) {
    s_current_effect = effect;
    if (effect == LED_EFFECT_NONE) {
        memset(s_leds, 0, sizeof(s_leds));
        led_show();
    }
}

void led_set(int index, led_color_t color) {
    if (index < 0 || index >= s_num_leds) return;
    if (s_led_mutex) xSemaphoreTake(s_led_mutex, portMAX_DELAY);
    s_leds[index] = color;
    if (s_led_mutex) xSemaphoreGive(s_led_mutex);
}

esp_err_t led_show(void) {
    if (!rmt_chan || !rmt_enc) return ESP_ERR_INVALID_STATE;
    // Mutex protects concurrent rmt_transmit from led_effect_task + led_task (audit RX#8)
    if (s_led_mutex) xSemaphoreTake(s_led_mutex, portMAX_DELAY);

    // 2.6.2: if strip looks disconnected, back off to one retry every 5s rather than
    // burning 50ms per call. Original code permanently disabled after 6 fails.
    if (s_rmt_fail_count >= LED_FAIL_BACKOFF_THRESHOLD) {
        if (xTaskGetTickCount() - s_last_fail_tick < LED_RETRY_INTERVAL_TICKS) {
            if (s_led_mutex) xSemaphoreGive(s_led_mutex);
            return ESP_ERR_INVALID_STATE;
        }
        s_last_fail_tick = xTaskGetTickCount();  // mark this attempt
    }

    build_rmt_buf();
    esp_err_t err = rmt_transmit(rmt_chan, rmt_enc, s_rmt_buf,
                                 (s_num_leds * 24 + 1) * sizeof(rmt_symbol_word_t),
                                 &tx_cfg);
    if (err == ESP_OK) {
        err = rmt_tx_wait_all_done(rmt_chan, pdMS_TO_TICKS(50));
        if (err != ESP_OK) {
            s_rmt_fail_count++;
            s_last_fail_tick = xTaskGetTickCount();
            s_strip_present = false;
            if (s_rmt_fail_count == LED_FAIL_BACKOFF_THRESHOLD)
                ESP_LOGW(TAG, "RMT failing — strip likely disconnected. Backing off, will retry every 5s.");
        } else {
            if (s_rmt_fail_count > 0) {
                ESP_LOGI(TAG, "RMT recovered after %d failure(s) — strip is back.", s_rmt_fail_count);
            }
            s_rmt_fail_count = 0;
            s_strip_present = true;
        }
    }
    if (s_led_mutex) xSemaphoreGive(s_led_mutex);
    return err;
}

void led_set_brightness(uint8_t brightness) {
    if (s_led_mutex) xSemaphoreTake(s_led_mutex, portMAX_DELAY);
    s_brightness = brightness;
    if (s_led_mutex) xSemaphoreGive(s_led_mutex);
}

void led_get_status(led_status_t *out) {
    if (!out) return;
    out->initialized = s_initialized;
    out->present     = s_strip_present;
    out->fail_count  = s_rmt_fail_count;
    out->num_leds    = s_num_leds;
    out->brightness  = s_brightness;
}

void led_reinit(int num_leds, uint8_t brightness) {
    if (num_leds < 1) num_leds = 1;
    if (num_leds > MAX_LEDS) num_leds = MAX_LEDS;

    int old_count = s_num_leds;

    // If shrinking, blank the soon-to-be-unused LEDs at the OLD frame size first
    // so trailing LEDs go dark cleanly before we shorten the frame.
    if (num_leds < old_count) {
        if (s_led_mutex) xSemaphoreTake(s_led_mutex, portMAX_DELAY);
        memset(s_leds, 0, sizeof(s_leds));
        if (s_led_mutex) xSemaphoreGive(s_led_mutex);
        led_show();  // sends a full old-size all-black frame
    }

    if (s_led_mutex) xSemaphoreTake(s_led_mutex, portMAX_DELAY);
    s_num_leds   = num_leds;
    s_brightness = brightness;
    if (s_led_mutex) xSemaphoreGive(s_led_mutex);
    // Caller is expected to repaint via the registry/effect task, but a refresh
    // here ensures the new size + brightness shows up even if no other path runs.
    led_show();
}
