Techposts/TankSync/firmware/Receiver-ESP32-DevKit/components/mqtt_client/mqtt_manager.c

/**
 * mqtt_manager implementation
 */

#include "mqtt_manager.h"
#include "mqtt_client.h"        // ESP-IDF MQTT (component: mqtt)
#include "esp_crt_bundle.h"    // TLS cert bundle for MQTTS
#include "transmitter_registry.h"
#include "wifi_manager.h"
#include "lora_rylr998.h"
#include "ota_manager.h"        // PWA-triggered OTA via cmd/ota_check, cmd/ota_install
#include "led_ws2812.h"         // PWA-triggered LED config via cmd/led_get, cmd/led_set
#include "buzzer.h"             // PWA-triggered buzzer config via cmd/buzzer_get, cmd/buzzer_set, cmd/buzzer_test
#include "esp_log.h"
#include "esp_mac.h"
#include "esp_timer.h"
#include "esp_event.h"
#include "nvs_flash.h"
#include "nvs.h"
#include "freertos/FreeRTOS.h"
#include "freertos/task.h"
#include "cJSON.h"              // For set_config command payload parsing
#include <string.h>
#include <stdio.h>
#include <stdlib.h>

static const char *TAG = "mqtt";

#define NVS_NS          "mqtt"
#define MAX_TOPIC_LEN   128
#define MAX_PAYLOAD_LEN 512

static esp_mqtt_client_handle_t s_client = NULL;
static mqtt_mgr_status_t        s_status = MQTT_ST_DISABLED;
static mqtt_mgr_config_t        s_cfg    = {0};
static char                     s_dev_id[13] = {0};  // 12-char hex + null

// ── Device ID ─────────────────────────────────────────────────────────────────
static void init_device_id(void) {
    uint8_t mac[6];
    esp_read_mac(mac, ESP_MAC_WIFI_STA);
    snprintf(s_dev_id, sizeof(s_dev_id), "%02x%02x%02x%02x%02x%02x",
             mac[0], mac[1], mac[2], mac[3], mac[4], mac[5]);
}

const char *mqtt_manager_device_id(void) { return s_dev_id; }

// ── NVS helpers ───────────────────────────────────────────────────────────────
static void load_config(void) {
    nvs_handle_t h;
    if (nvs_open(NVS_NS, NVS_READONLY, &h) != ESP_OK) return;

    size_t len = sizeof(s_cfg.host);
    nvs_get_str(h, "host", s_cfg.host, &len);
    uint16_t port = MQTT_DEFAULT_PORT;
    nvs_get_u16(h, "port", &port);
    s_cfg.port = port;
    len = sizeof(s_cfg.user);
    nvs_get_str(h, "user", s_cfg.user, &len);
    len = sizeof(s_cfg.pass);
    nvs_get_str(h, "pass", s_cfg.pass, &len);
    uint8_t en = 0, ha = 0;
    nvs_get_u8(h, "enabled", &en);
    nvs_get_u8(h, "ha_disc", &ha);
    s_cfg.enabled      = (en != 0);
    s_cfg.ha_discovery = (ha != 0);
    nvs_close(h);
}

static esp_err_t save_config_nvs(const mqtt_mgr_config_t *cfg) {
    nvs_handle_t h;
    esp_err_t err = nvs_open(NVS_NS, NVS_READWRITE, &h);
    if (err != ESP_OK) return err;
    nvs_set_str(h, "host",    cfg->host);
    nvs_set_u16(h, "port",    cfg->port ? cfg->port : MQTT_DEFAULT_PORT);
    nvs_set_str(h, "user",    cfg->user);
    if (strlen(cfg->pass) > 0) nvs_set_str(h, "pass", cfg->pass); // only update if provided
    nvs_set_u8 (h, "enabled", cfg->enabled ? 1 : 0);
    nvs_set_u8 (h, "ha_disc", cfg->ha_discovery ? 1 : 0);
    err = nvs_commit(h);
    nvs_close(h);
    return err;
}

// ── Topic builder ─────────────────────────────────────────────────────────────
static void make_topic(char *buf, size_t len,
                        const char *slug, const char *field) {
    if (slug) {
        snprintf(buf, len, MQTT_TOPIC_PREFIX "/%s/%s/%s", s_dev_id, slug, field);
    } else {
        snprintf(buf, len, MQTT_TOPIC_PREFIX "/%s/%s", s_dev_id, field);
    }
}

static void pub(const char *topic, const char *payload, int retain) {
    if (!s_client || s_status != MQTT_ST_CONNECTED) return;
    esp_mqtt_client_publish(s_client, topic, payload, 0, 1, retain);
}

// ── MQTT command handler ─────────────────────────────────────────────────────
// Handles commands received on tanksync/{device_id}/cmd/{command}
// Publishes results to tanksync/{device_id}/cmd_result/{command}
static void handle_cmd(const char *command, const char *payload) {
    char result_topic[MAX_TOPIC_LEN];
    char result[MAX_PAYLOAD_LEN];

    if (strcmp(command, "pair_start") == 0) {
        lora_set_pairing_mode(true);
        make_topic(result_topic, sizeof(result_topic), "cmd_result", "pair_start");
        pub(result_topic, "{\"ok\":true,\"status\":\"searching\"}", 0);
        ESP_LOGI(TAG, "CMD: pair_start");

    } else if (strcmp(command, "pair_stop") == 0) {
        lora_set_pairing_mode(false);
        make_topic(result_topic, sizeof(result_topic), "cmd_result", "pair_stop");
        pub(result_topic, "{\"ok\":true}", 0);
        ESP_LOGI(TAG, "CMD: pair_stop");

    } else if (strcmp(command, "remove_tx") == 0) {
        // Remove a transmitter from the registry. Payload: {"addr": <uint16>}.
        // Calls registry_remove() which soft-deletes (tombstones the entry) so
        // a returning TX with the same MAC can be resurrected via PAIR_REQ.
        // Cloud invokes this when the PWA deletes a tank — without it, the
        // cloud-side DB deletion would not propagate to the hub and the tank
        // would reappear on the next PWA refresh from the truth source.
        cJSON *j = cJSON_Parse(payload);
        uint16_t addr = j ? (uint16_t)cJSON_GetNumberValue(cJSON_GetObjectItem(j, "addr")) : 0;
        if (j) cJSON_Delete(j);
        make_topic(result_topic, sizeof(result_topic), "cmd_result", "remove_tx");
        if (addr == 0) {
            pub(result_topic, "{\"ok\":false,\"error\":\"missing addr\"}", 0);
            ESP_LOGW(TAG, "CMD remove_tx: missing addr in payload");
        } else {
            // Clear retained broker state BEFORE registry_remove so the
            // (slug = "tank_<addr>") topics are still meaningful at clear-time.
            // mqtt_unpublish_tank is a no-op if MQTT is down; safe to always call.
            mqtt_unpublish_tank(addr);
            if (registry_remove(addr)) {
                // Republish the manifest so cloud can prune the orphan even
                // without seeing the per-topic empty payloads (defense-in-depth).
                mqtt_publish_registry();
                snprintf(result, sizeof(result), "{\"ok\":true,\"addr\":%d}", addr);
                pub(result_topic, result, 0);
                ESP_LOGI(TAG, "CMD remove_tx: addr=%d removed (tombstoned for MAC restore)", addr);
            } else {
                snprintf(result, sizeof(result), "{\"ok\":false,\"addr\":%d,\"error\":\"not found\"}", addr);
                pub(result_topic, result, 0);
                ESP_LOGW(TAG, "CMD remove_tx: addr=%d not in registry", addr);
            }
        }

    } else if (strcmp(command, "pair_status") == 0) {
        bool active = false; uint16_t addr = 0; char name[TX_NAME_MAX] = {0}; int time_left = 0;
        lora_get_pairing_state(&active, &addr, name, &time_left);
        bool paired = !active && addr > 0;
        snprintf(result, sizeof(result),
            "{\"active\":%s,\"paired\":%s,\"addr\":%d,\"name\":\"%s\",\"time_left\":%d}",
            active ? "true" : "false", paired ? "true" : "false",
            addr, name, time_left);
        make_topic(result_topic, sizeof(result_topic), "cmd_result", "pair_status");
        pub(result_topic, result, 0);

    } else if (strcmp(command, "refresh") == 0) {
        mqtt_publish_system();
        int n = registry_count();
        for (int i = 0; i < n; i++) mqtt_publish_tank(i);
        make_topic(result_topic, sizeof(result_topic), "cmd_result", "refresh");
        pub(result_topic, "{\"ok\":true}", 0);
        ESP_LOGI(TAG, "CMD: refresh");

    } else if (strcmp(command, "set_config") == 0) {
        // Cloud-side edit: payload is the same JSON shape that POST /api/transmitters
        // accepts on the local web UI. Mirrors that handler so PWA edits and web UI
        // edits go through the identical registry + LoRa-CONFIG path. Worked-around
        // root cause: cloud server cannot HTTP-POST to a 192.x receiver from a
        // public droplet; MQTT command channel works through any NAT.
        make_topic(result_topic, sizeof(result_topic), "cmd_result", "set_config");
        cJSON *j = cJSON_Parse(payload);
        if (!j) {
            pub(result_topic, "{\"ok\":false,\"err\":\"bad_json\"}", 0);
            ESP_LOGW(TAG, "CMD set_config: parse failed");
            return;
        }
        uint16_t addr = (uint16_t)cJSON_GetNumberValue(cJSON_GetObjectItem(j, "addr"));
        const char *name_ptr = cJSON_GetStringValue(cJSON_GetObjectItem(j, "name"));
        char name_buf[TX_NAME_MAX] = {0};
        if (name_ptr) { strncpy(name_buf, name_ptr, TX_NAME_MAX - 1); }
        int min_d  = (int)cJSON_GetNumberValue(cJSON_GetObjectItem(j, "min_dist"));
        int max_d  = (int)cJSON_GetNumberValue(cJSON_GetObjectItem(j, "max_dist"));
        float cap  = (float)cJSON_GetNumberValue(cJSON_GetObjectItem(j, "capacity"));
        uint32_t sleep_s = (uint32_t)cJSON_GetNumberValue(cJSON_GetObjectItem(j, "sleep_s"));
        uint8_t  samples = (uint8_t)cJSON_GetNumberValue(cJSON_GetObjectItem(j, "samples"));
        cJSON *pwr_j = cJSON_GetObjectItem(j, "lora_pwr");
        uint8_t  pwr = pwr_j ? (uint8_t)cJSON_GetNumberValue(pwr_j) : 0;
        if (pwr > 22) pwr = 22;
        // Optional sensor_kind ("sr04" | "ld2413"). Absent or empty = leave
        // whatever the TX currently has. Validation is in registry_set_sensor_kind.
        const char *sk_ptr = cJSON_GetStringValue(cJSON_GetObjectItem(j, "sensor_kind"));
        char sk_buf[12] = {0};
        if (sk_ptr) { strncpy(sk_buf, sk_ptr, sizeof(sk_buf) - 1); }
        cJSON_Delete(j);

        const char *name = name_ptr ? name_buf : NULL;

        if (addr == 0) {
            pub(result_topic, "{\"ok\":false,\"err\":\"bad_addr\"}", 0);
            return;
        }
        bool updated = registry_update(addr, name, min_d, max_d, cap);
        if (!updated && registry_add(addr, name, min_d, max_d, cap) < 0) {
            pub(result_topic, "{\"ok\":false,\"err\":\"registry_full\"}", 0);
            return;
        }
        if (sleep_s >= 60) {
            registry_set_remote_config(addr, sleep_s, samples > 0 ? samples : 5, pwr);
        }
        if (sk_buf[0]) {
            if (!registry_set_sensor_kind(addr, sk_buf)) {
                pub(result_topic, "{\"ok\":false,\"err\":\"bad_sensor_kind\"}", 0);
                return;
            }
        }
        // Republish config immediately so cloud sees the new state without waiting
        // for the next periodic publish cycle.
        int idx = registry_find(addr);
        if (idx >= 0) mqtt_publish_tank(idx);

        pub(result_topic, "{\"ok\":true}", 0);
        ESP_LOGI(TAG, "CMD set_config: addr=%u sleep=%lu samples=%u pwr=%u sensor=%s",
                 (unsigned)addr, (unsigned long)sleep_s, (unsigned)samples, (unsigned)pwr,
                 sk_buf[0] ? sk_buf : "(unchanged)");

    } else if (strcmp(command, "ota_check") == 0) {
        // PWA-triggered manifest check. Non-blocking — actual fetch runs in
        // ota_task within ~60s. PWA polls cmd/ota_status to learn the result.
        make_topic(result_topic, sizeof(result_topic), "cmd_result", "ota_check");
        esp_err_t r = ota_manager_check_github();
        if (r == ESP_OK) {
            pub(result_topic, "{\"ok\":true,\"queued\":true}", 0);
        } else if (r == ESP_ERR_INVALID_STATE) {
            pub(result_topic, "{\"ok\":false,\"err\":\"busy\"}", 0);
        } else {
            snprintf(result, sizeof(result),
                     "{\"ok\":false,\"err\":\"%s\"}", esp_err_to_name(r));
            pub(result_topic, result, 0);
        }
        ESP_LOGI(TAG, "CMD ota_check: %s", esp_err_to_name(r));

    } else if (strcmp(command, "ota_status") == 0) {
        // Snapshot the OTA state for PWA polling. Status enum mirrors
        // ota_status_t in ota_manager.h.
        make_topic(result_topic, sizeof(result_topic), "cmd_result", "ota_status");
        ota_state_t st;
        ota_manager_get_state(&st);
        const char *st_str =
            st.status == OTA_ST_IDLE        ? "idle"        :
            st.status == OTA_ST_CHECKING    ? "checking"    :
            st.status == OTA_ST_AVAILABLE   ? "available"   :
            st.status == OTA_ST_DOWNLOADING ? "downloading" :
            st.status == OTA_ST_DONE        ? "done"        :
            st.status == OTA_ST_UP_TO_DATE  ? "up_to_date"  :
            st.status == OTA_ST_ERROR       ? "error"       : "unknown";
        // Escape-safe minimal JSON; latest_version + error_msg are bounded
        // strings (32 / 128) and never contain quotes in practice (set by
        // do_github_check using snprintf with controlled inputs).
        snprintf(result, sizeof(result),
            "{\"ok\":true,\"status\":\"%s\",\"current\":\"%s\",\"latest\":\"%s\",\"progress\":%d,\"error\":\"%s\"}",
            st_str, FIRMWARE_VERSION, st.latest_version,
            st.progress_pct, st.error_msg);
        pub(result_topic, result, 0);

    } else if (strcmp(command, "ota_install") == 0) {
        // Trigger flash from cached download_url (set by prior ota_check).
        // Spawns a one-shot task — the flash itself takes ~30s and would
        // otherwise stall the MQTT event loop.
        make_topic(result_topic, sizeof(result_topic), "cmd_result", "ota_install");
        esp_err_t r = ota_manager_request_install();
        if (r == ESP_OK) {
            pub(result_topic, "{\"ok\":true,\"installing\":true}", 0);
        } else if (r == ESP_ERR_INVALID_STATE) {
            pub(result_topic, "{\"ok\":false,\"err\":\"no_update_or_busy\"}", 0);
        } else {
            snprintf(result, sizeof(result),
                     "{\"ok\":false,\"err\":\"%s\"}", esp_err_to_name(r));
            pub(result_topic, result, 0);
        }
        ESP_LOGI(TAG, "CMD ota_install: %s", esp_err_to_name(r));

    } else if (strcmp(command, "led_get") == 0) {
        // 2.6.3: PWA polls current LED config + driver health for the Lights & Display panel.
        make_topic(result_topic, sizeof(result_topic), "cmd_result", "led_get");
        uint8_t count = 2, bright = 50;
        nvs_handle_t h;
        if (nvs_open("system", NVS_READONLY, &h) == ESP_OK) {
            nvs_get_u8(h, "led_count", &count);
            nvs_get_u8(h, "led_bright", &bright);
            nvs_close(h);
        }
        led_status_t st; led_get_status(&st);
        cJSON *root = cJSON_CreateObject();
        cJSON_AddBoolToObject  (root, "ok",            true);
        cJSON_AddNumberToObject(root, "count",         count);
        cJSON_AddNumberToObject(root, "brightness",    bright);
        cJSON_AddBoolToObject  (root, "initialized",   st.initialized);
        cJSON_AddBoolToObject  (root, "strip_present", st.present);
        cJSON_AddNumberToObject(root, "fail_count",    st.fail_count);
        cJSON *cols = cJSON_AddArrayToObject(root, "tank_colors");
        int n = registry_count();
        for (int i = 0; i < n; i++) {
            tx_info_t info;
            if (registry_get_info(i, &info)) {
                cJSON *c = cJSON_CreateObject();
                cJSON_AddNumberToObject(c, "addr",      info.address);
                cJSON_AddStringToObject(c, "name",      info.name);
                cJSON_AddNumberToObject(c, "color_idx", info.led_color_idx);
                cJSON_AddItemToArray(cols, c);
            }
        }
        char *json = cJSON_PrintUnformatted(root); cJSON_Delete(root);
        pub(result_topic, json ? json : "{\"ok\":false}", 0);
        if (json) free(json);
        ESP_LOGI(TAG, "CMD led_get");

    } else if (strcmp(command, "led_set") == 0) {
        // Mirror of POST /api/led on the local web UI, callable from cloud PWA.
        make_topic(result_topic, sizeof(result_topic), "cmd_result", "led_set");
        cJSON *j = cJSON_Parse(payload);
        if (!j) { pub(result_topic, "{\"ok\":false,\"err\":\"bad_json\"}", 0); return; }

        uint8_t new_count = 0, new_bright = 0;
        nvs_handle_t h;
        if (nvs_open("system", NVS_READWRITE, &h) == ESP_OK) {
            cJSON *v;
            if ((v = cJSON_GetObjectItem(j, "count"))) {
                uint8_t c = (uint8_t)v->valueint;
                if (c == 2 || c == 8 || c == 24) {
                    nvs_set_u8(h, "led_count", c);
                    new_count = c;
                }
            }
            if ((v = cJSON_GetObjectItem(j, "brightness"))) {
                uint8_t b = (uint8_t)v->valueint;
                if (b > 0) { nvs_set_u8(h, "led_bright", b); new_bright = b; }
            }
            nvs_commit(h); nvs_close(h);
        }
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
